Aeurias/NadeshikoSlimeVR/Misc/cases8111X.jpg

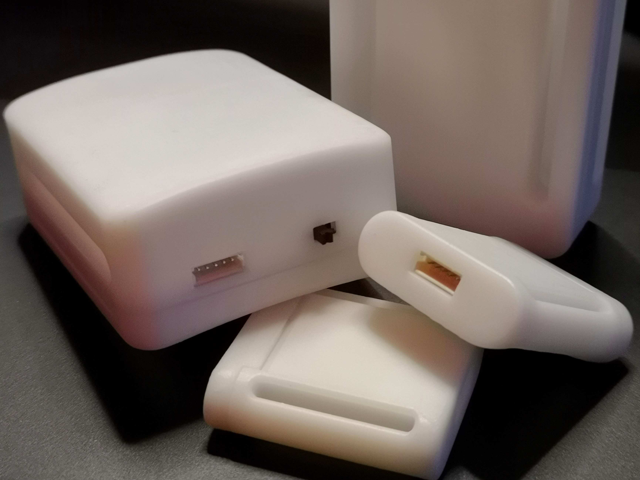
Misc/cases8111X.jpg
