Aeurias/NadeshikoSlimeVR/Misc/Extension-PCB-Front.png

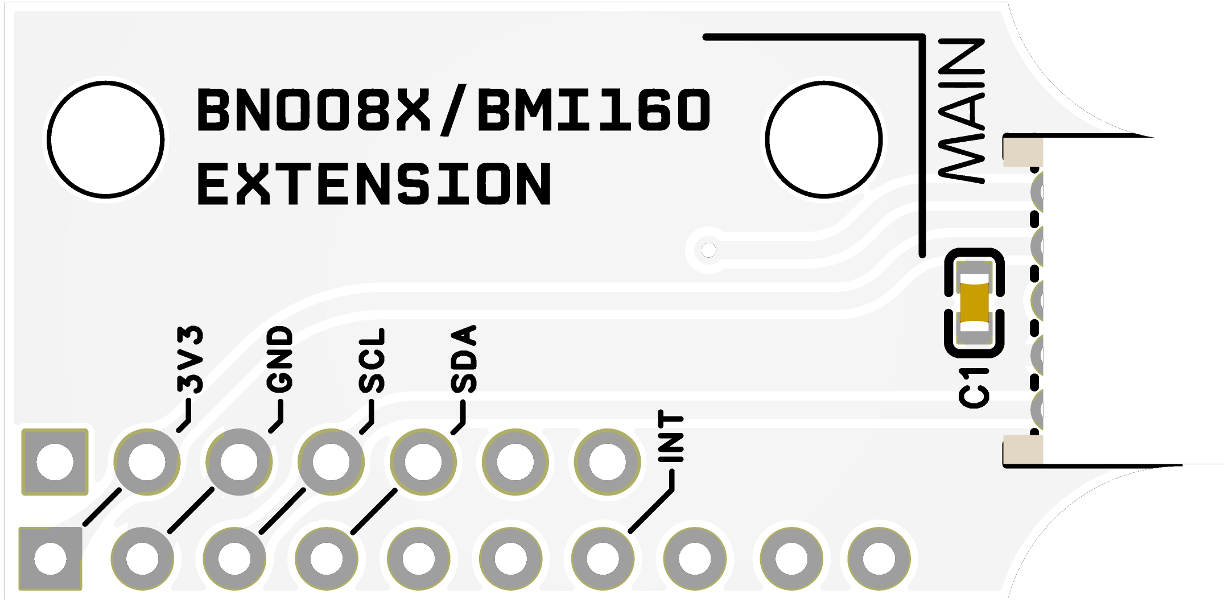
Misc/Extension-PCB-Front.png
