Aeurias/NadeshikoSlimeVR/Misc/PCBBack.png

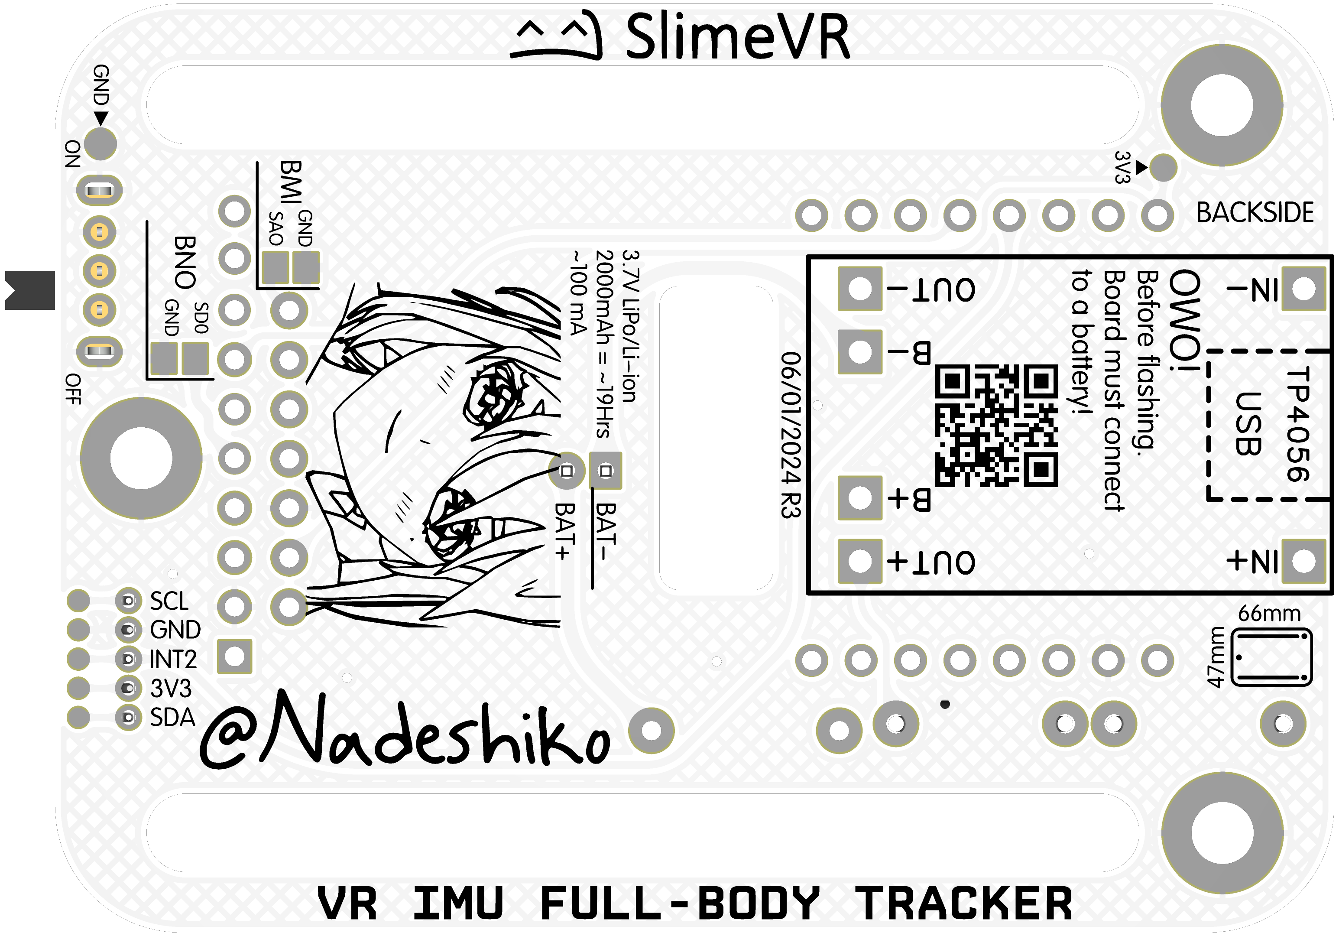
Misc/PCBBack.png
