Aeurias/NadeshikoSlimeVR/Misc/PCBFront.png

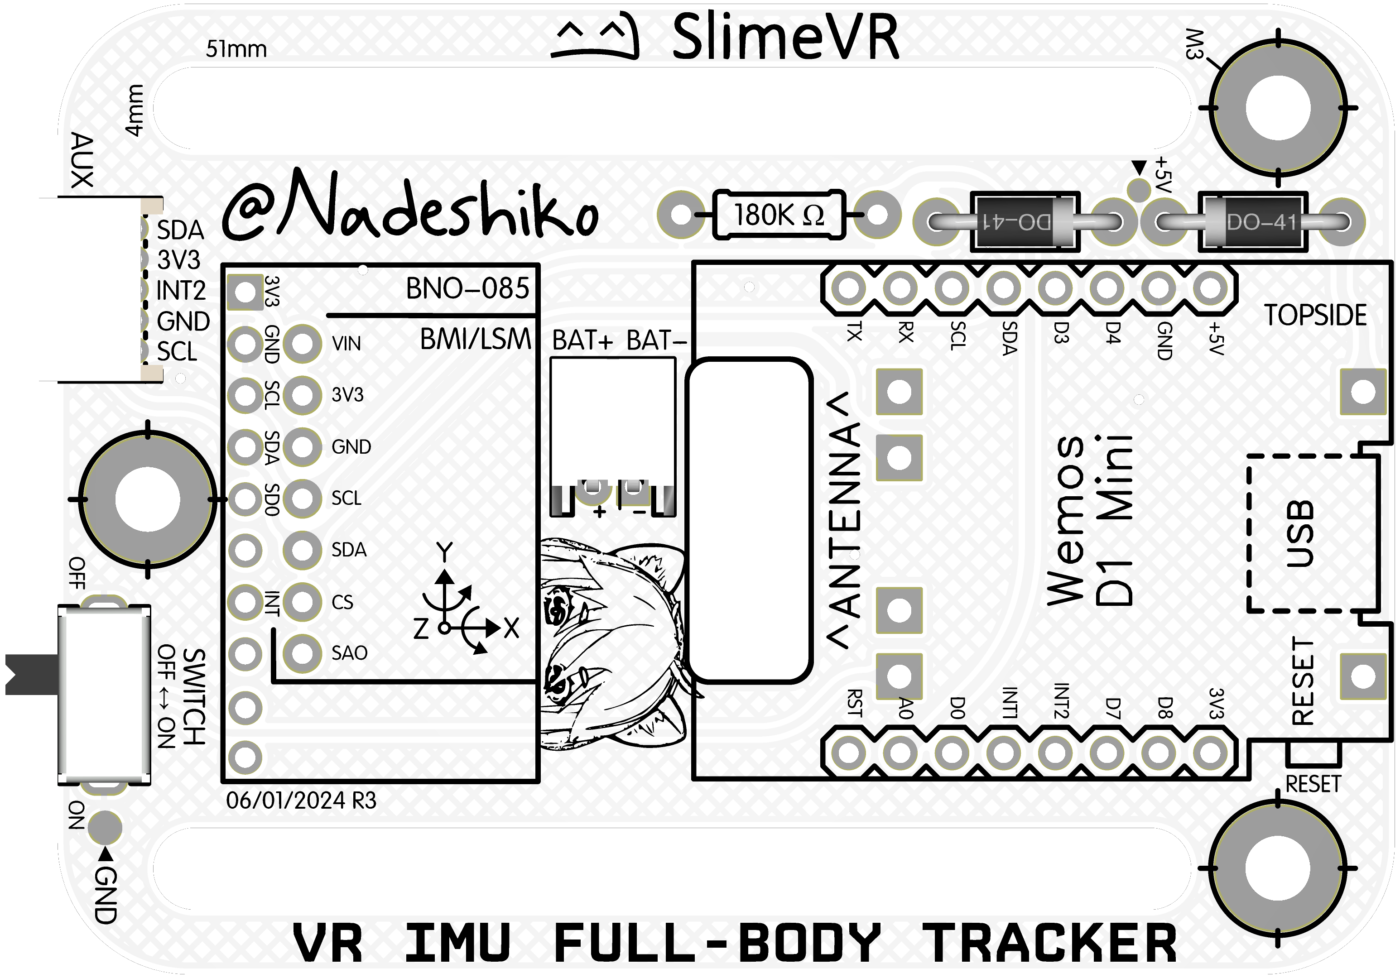
Misc/PCBFront.png
