Aeurias/NadeshikoSlimeVR/Misc/PlacementExample.png

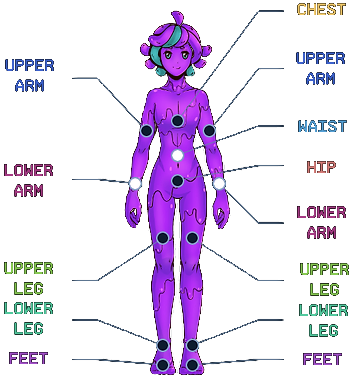
Misc/PlacementExample.png
