Aeurias/NadeshikoSlimeVR/Misc/PlacementOptions.png

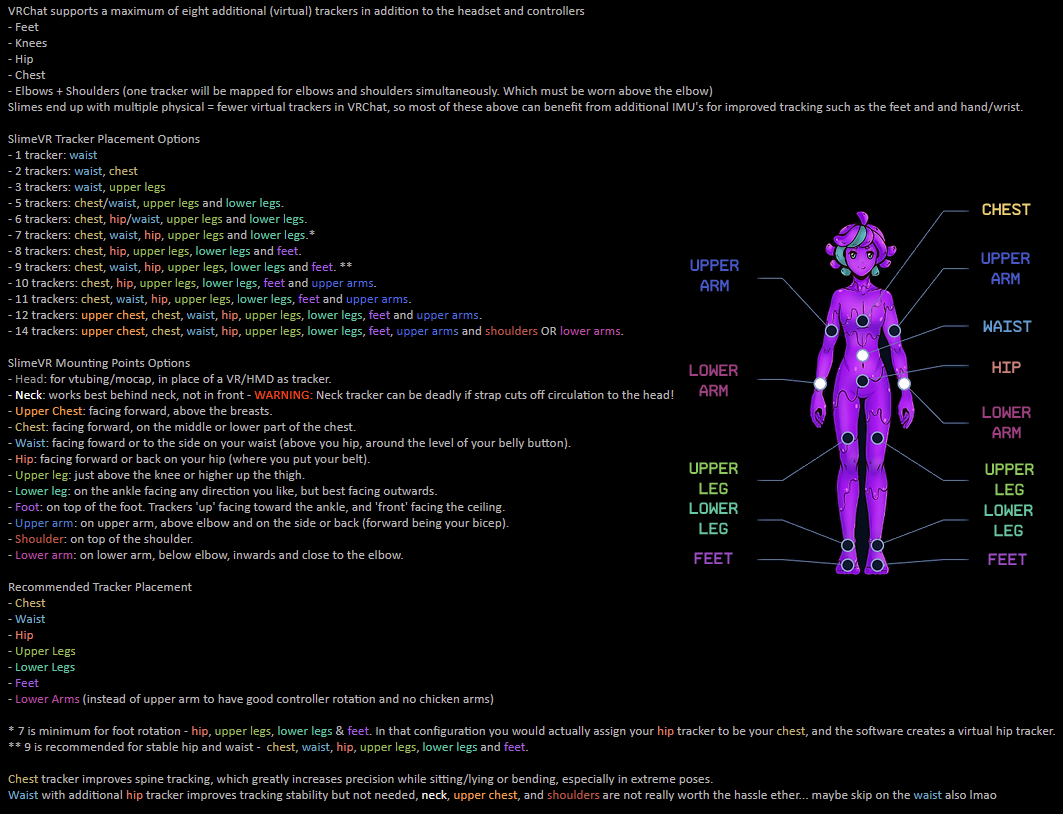
Misc/PlacementOptions.png
