Aeurias/NadeshikoSlimeVR/Misc/readmepreview1.png

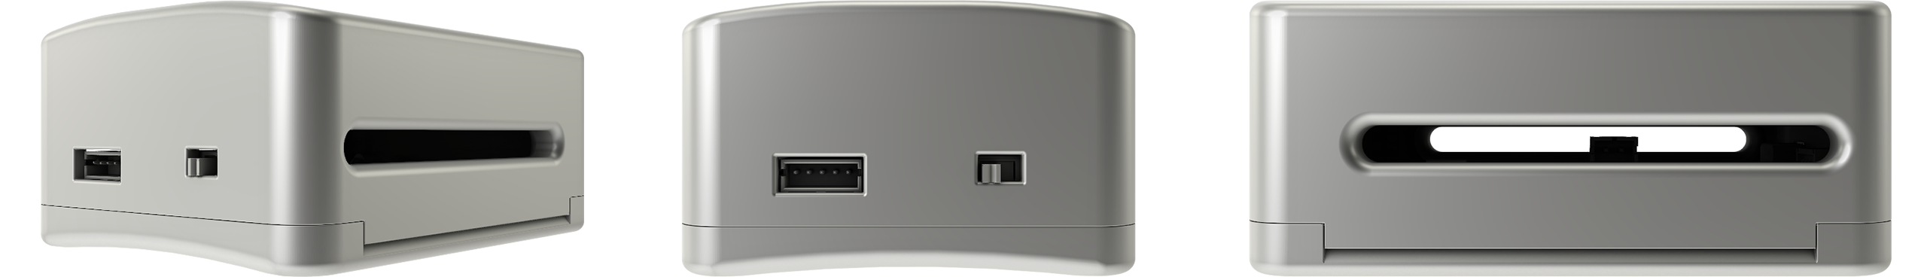
Misc/readmepreview1.png
