Aeurias/NadeshikoSlimeVR/R1/Previews/R1-18650-1.png

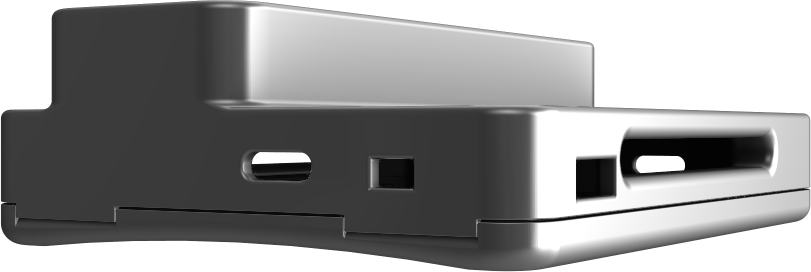
R1/Previews/R1-18650-1.png
