Aeurias/NadeshikoSlimeVR/R1/Previews/R1-18650-2.png

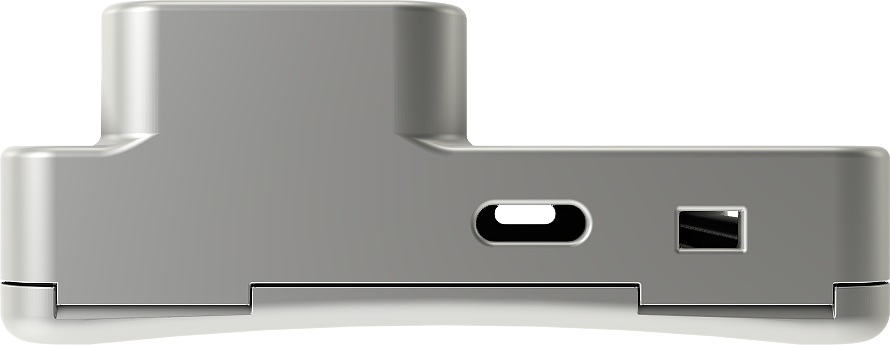
R1/Previews/R1-18650-2.png
