Aeurias/NadeshikoSlimeVR/R1/Previews/R1-18650-3.png

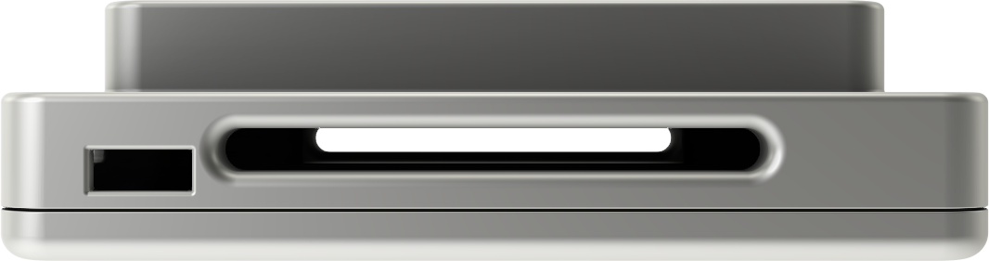
R1/Previews/R1-18650-3.png
