Aeurias/NadeshikoSlimeVR/R1/Previews/R1-LiPo-2.png

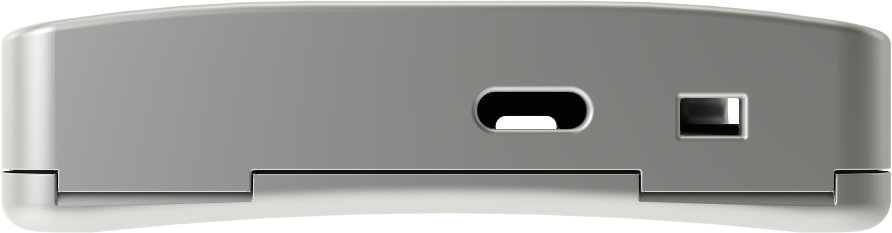
R1/Previews/R1-LiPo-2.png
