Aeurias/NadeshikoSlimeVR/R1/Previews/R1-LiPo-3.png

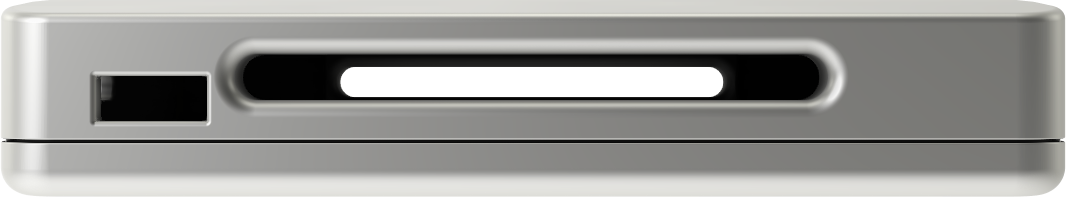
R1/Previews/R1-LiPo-3.png
