Aeurias/NadeshikoSlimeVR/R1/Previews/R1-PCB-Back.png

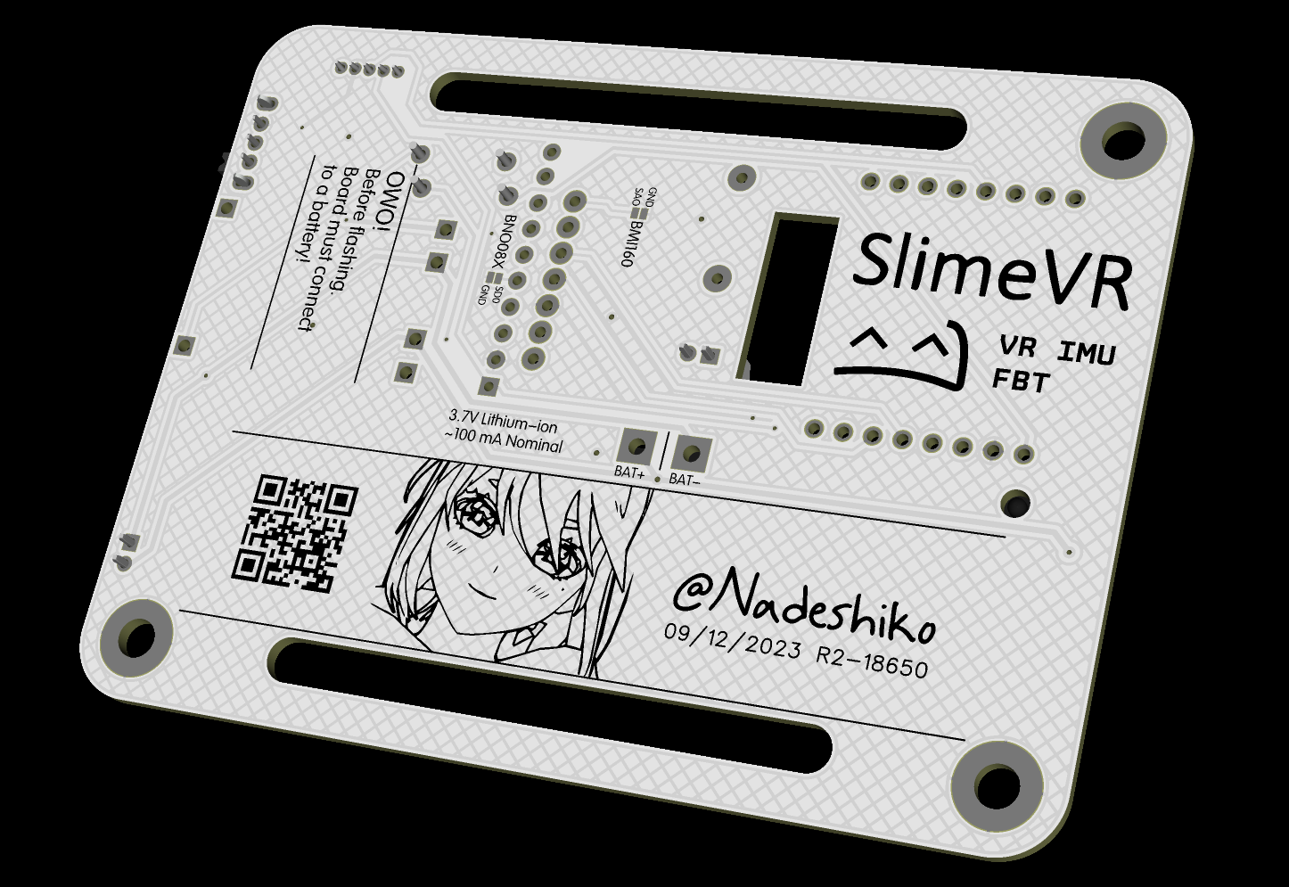
R1/Previews/R1-PCB-Back.png
