Aeurias/NadeshikoSlimeVR/R1/Previews/R1-PCB-Front.png

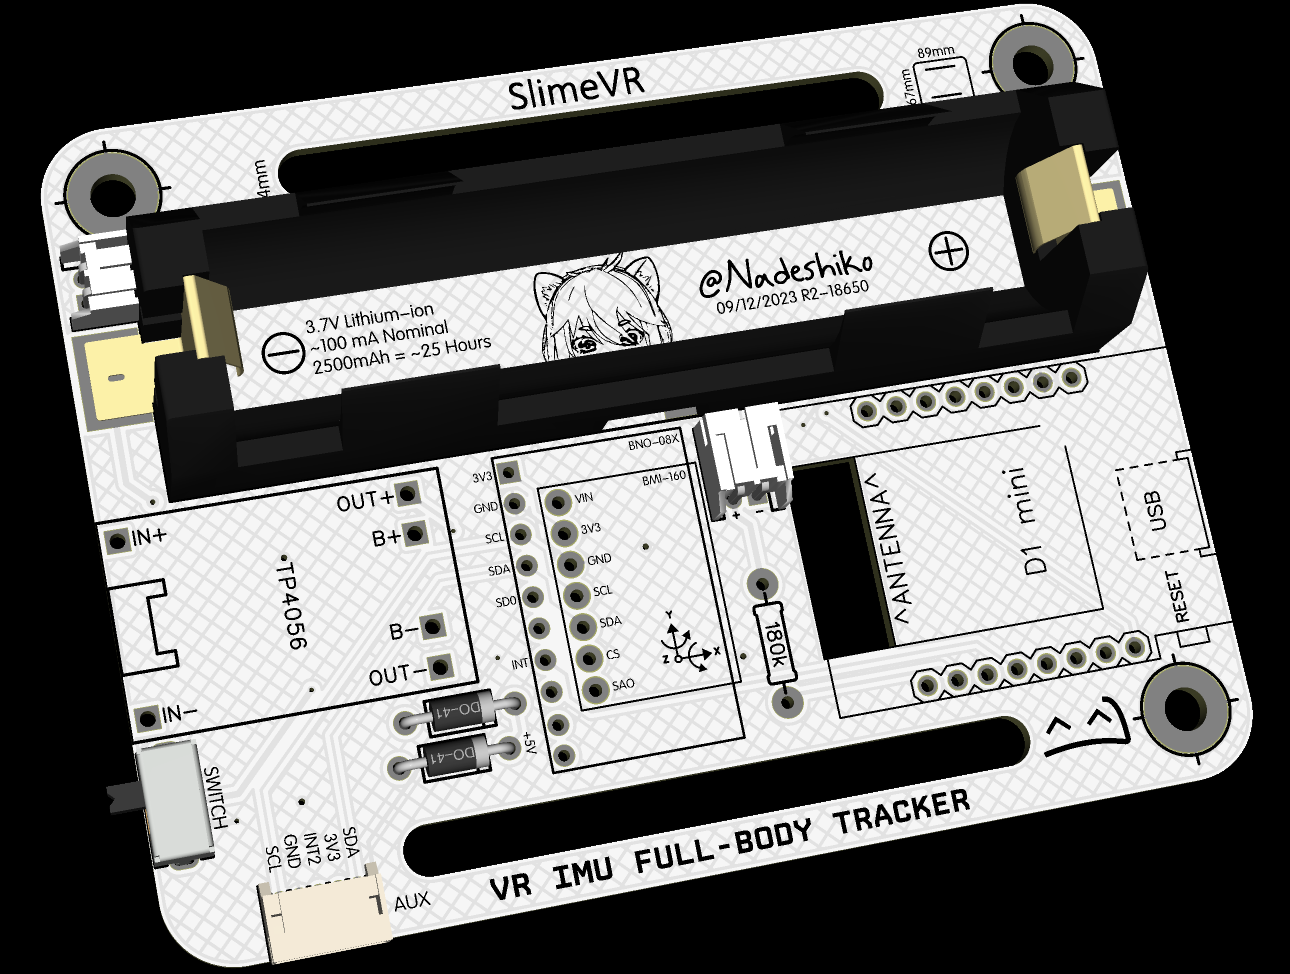
R1/Previews/R1-PCB-Front.png
