Aeurias/NadeshikoSlimeVR/R2 Mini/Previews/R2Mini-103450-3.png

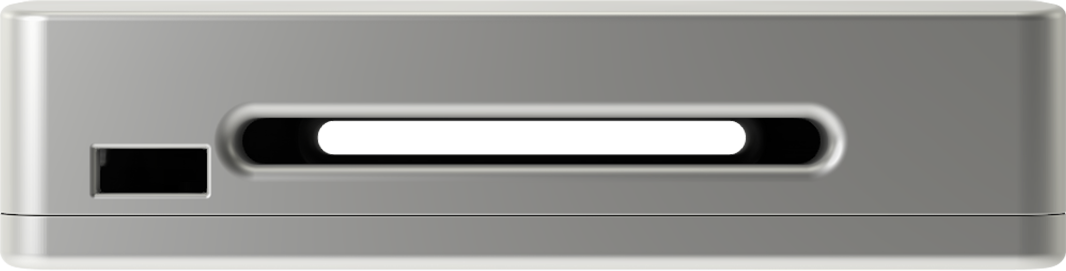
R2 Mini/Previews/R2Mini-103450-3.png
