Aeurias/NadeshikoSlimeVR/R2 Mini/Previews/R2Mini-503450-2.png

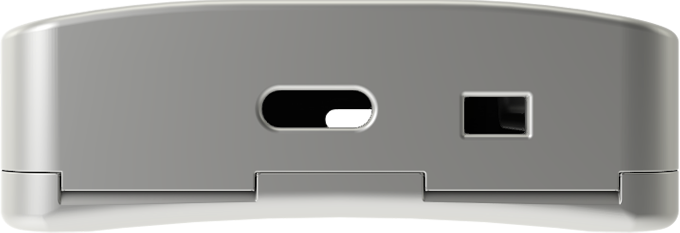
R2 Mini/Previews/R2Mini-503450-2.png
