Aeurias/NadeshikoSlimeVR/R2 Mini/Previews/R2Mini-503450-3.png

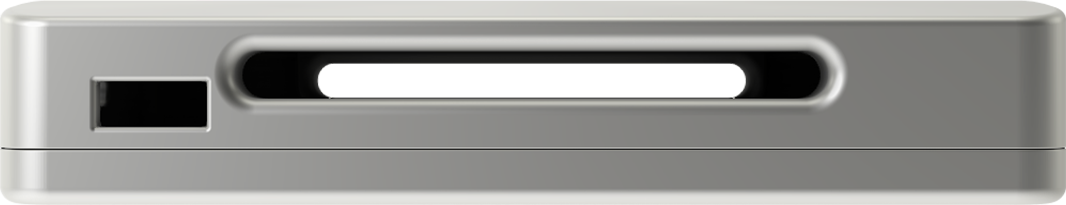
R2 Mini/Previews/R2Mini-503450-3.png
