Aeurias/NadeshikoSlimeVR/R2 Mini/Previews/R2Mini-PCB-Back.png

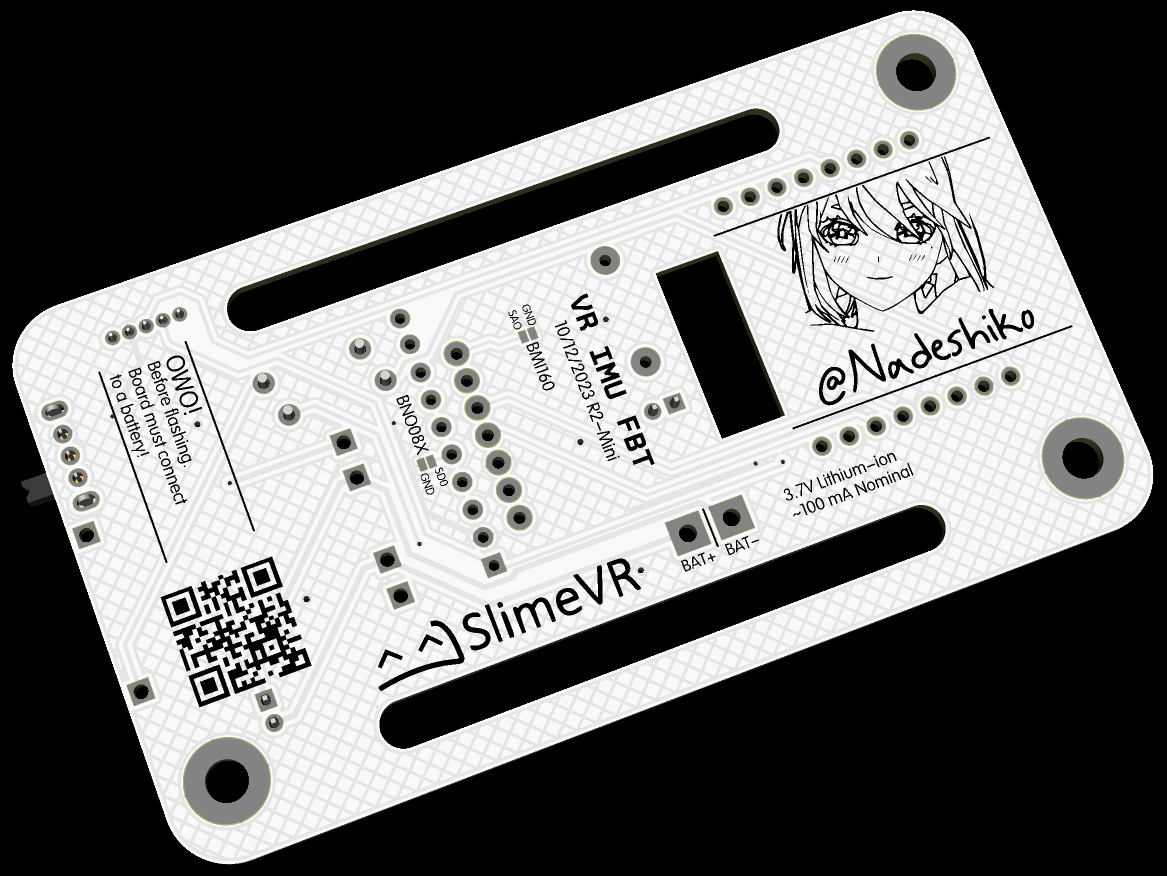
R2 Mini/Previews/R2Mini-PCB-Back.png
