Aeurias/NadeshikoSlimeVR/R2 Mini/Previews/R2Mini-PCB-Front.png

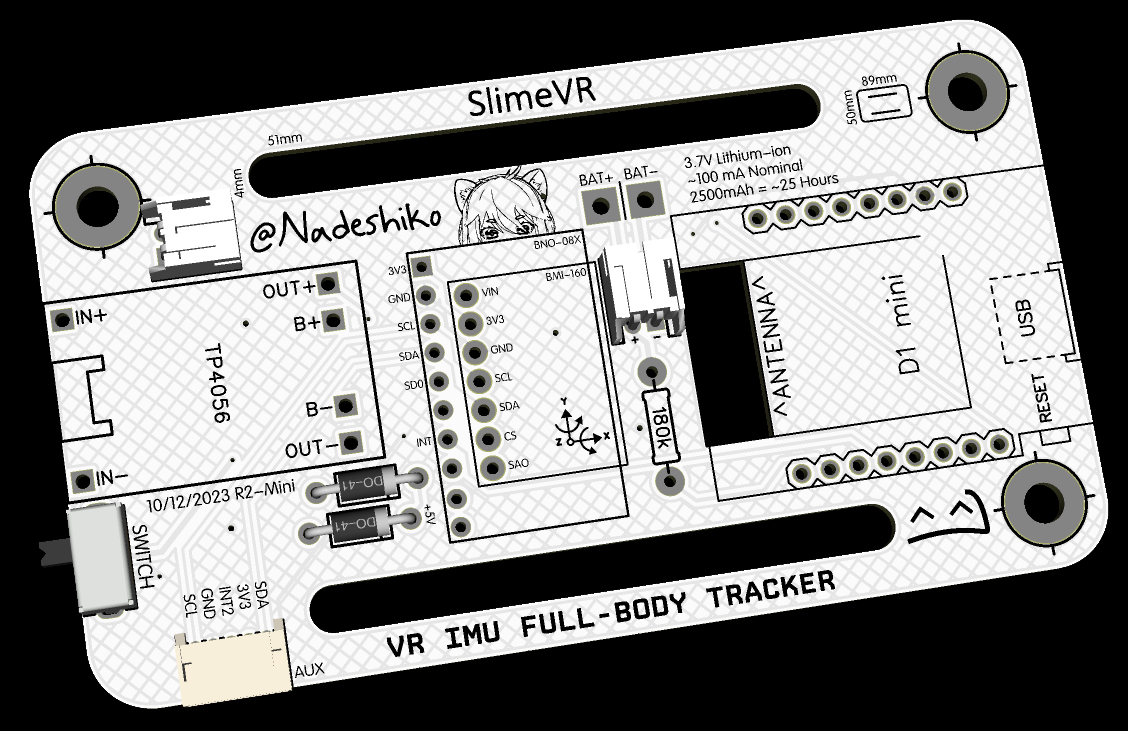
R2 Mini/Previews/R2Mini-PCB-Front.png
