Aeurias/NadeshikoSlimeVR/Tracker Extension/Previews/Extension-1.png

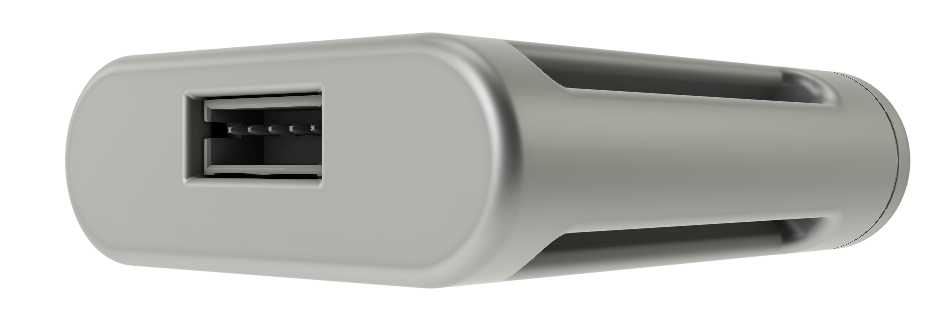
Tracker Extension/Previews/Extension-1.png
