Aeurias/NadeshikoSlimeVR/Tracker Extension/Previews/Extension-2.png

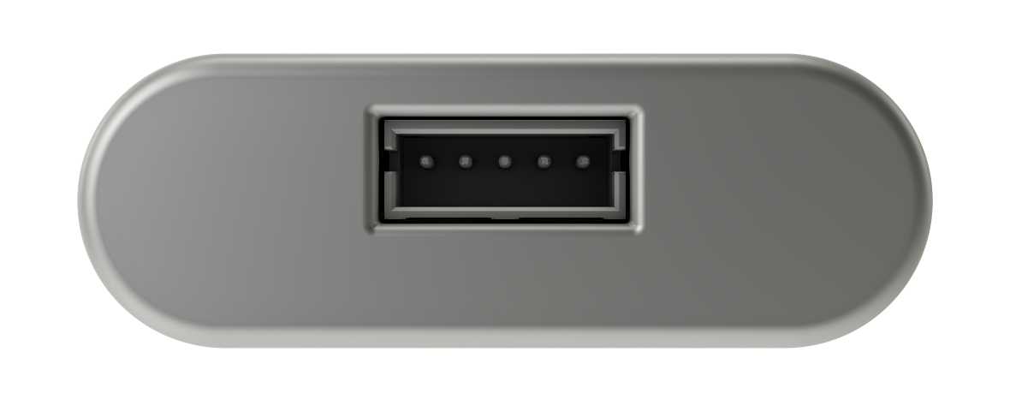
Tracker Extension/Previews/Extension-2.png
