Aeurias/NadeshikoSlimeVR/Tracker Extension/Previews/Extension-3.png

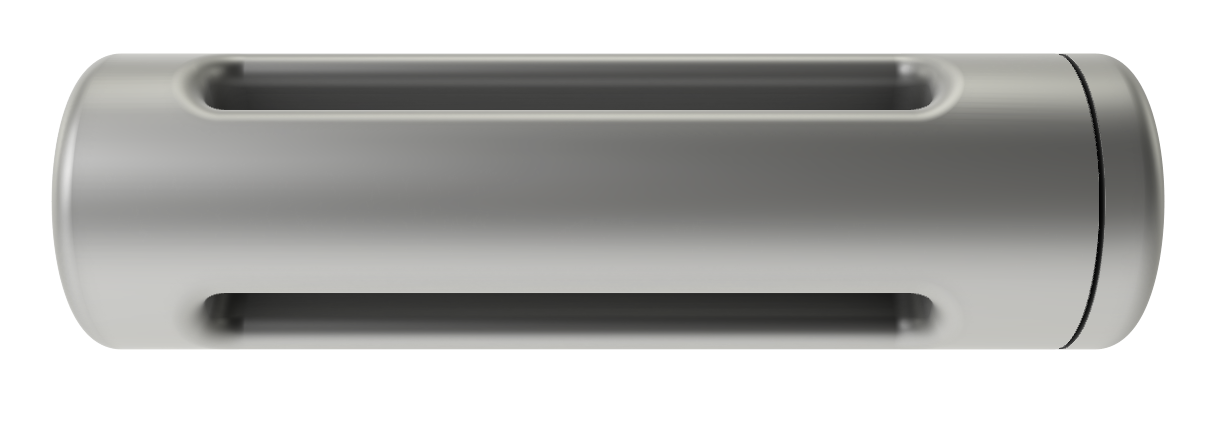
Tracker Extension/Previews/Extension-3.png
