Aeurias/NadeshikoSlimeVR/Tracker Extension/Previews/SlimeVRNadeshikoExtension_PREVIEW-1.png

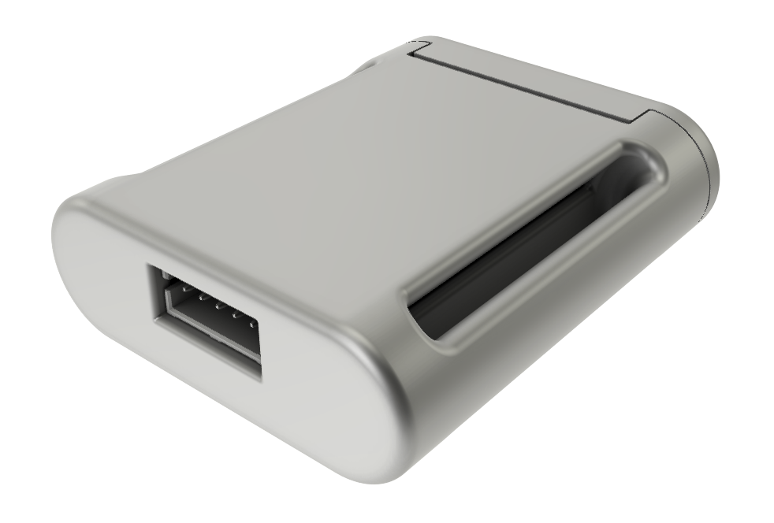
Tracker Extension/Previews/SlimeVRNadeshikoExtension_PREVIEW-1.png
