Aeurias/NadeshikoSlimeVR/Tracker Extension/Previews/SlimeVRNadeshikoExtension_PREVIEW-2.png

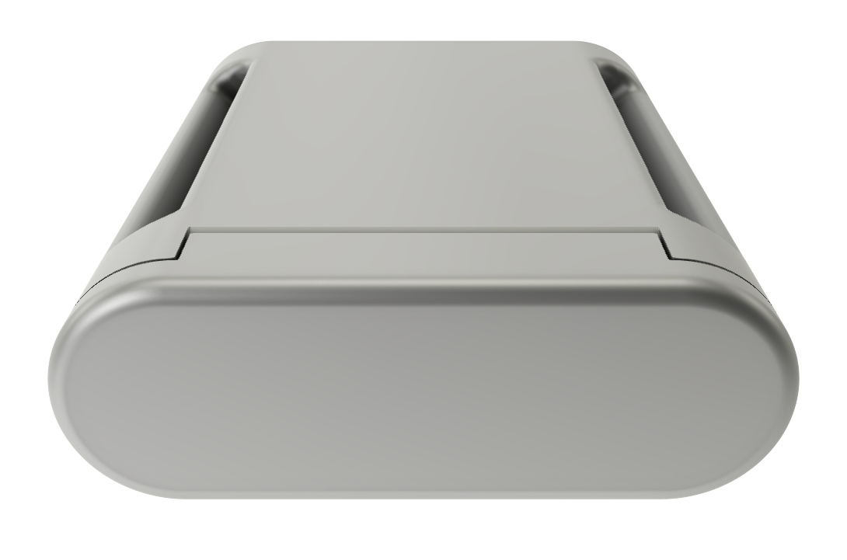
Tracker Extension/Previews/SlimeVRNadeshikoExtension_PREVIEW-2.png
