Aeurias/NadeshikoSlimeVR/Tracker Main/Previews/Back.png

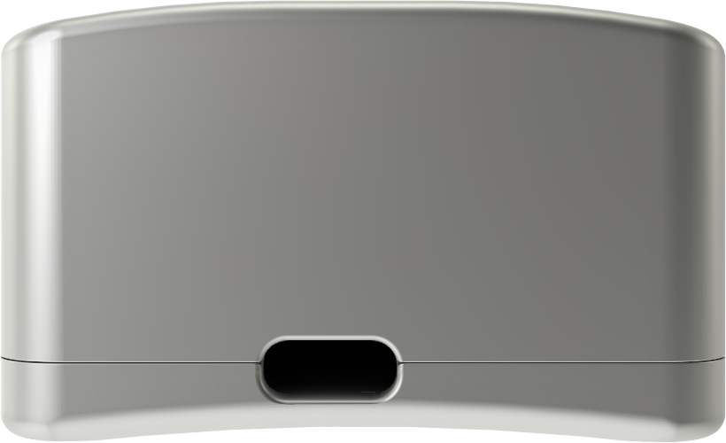
Tracker Main/Previews/Back.png
