Aeurias/NadeshikoSlimeVR/Tracker Main/Previews/CAD.jpg

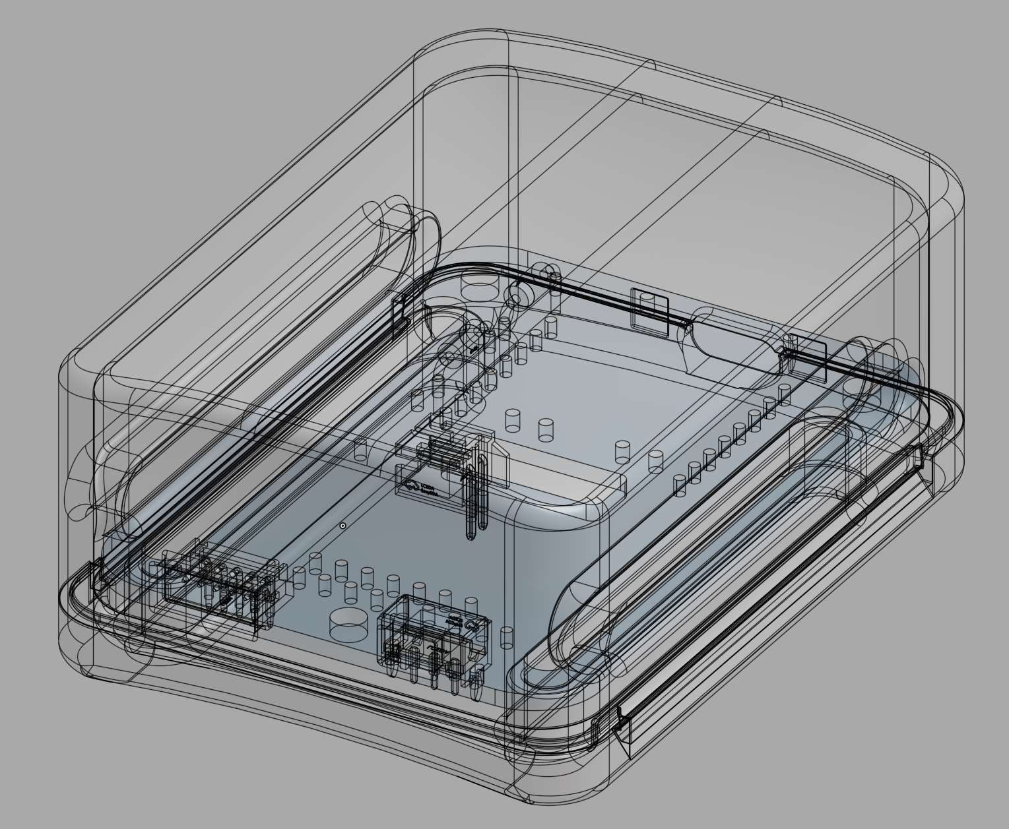
Tracker Main/Previews/CAD.jpg
