Aeurias/NadeshikoSlimeVR/Tracker Main/Previews/Front.png

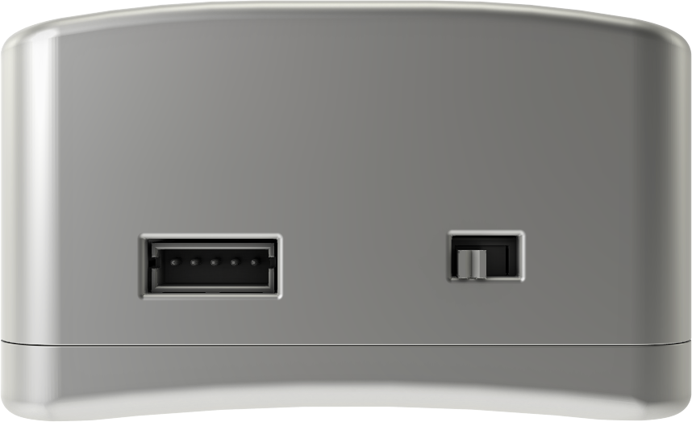
Tracker Main/Previews/Front.png
