Aeurias/NadeshikoSlimeVR/Tracker Main/Previews/FrontRight.png

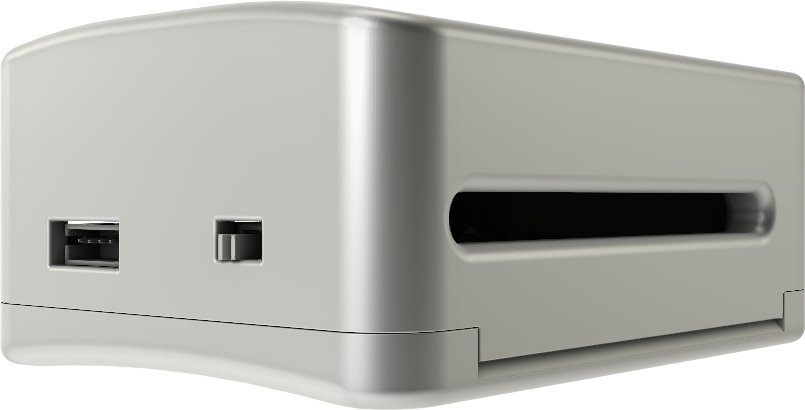
Tracker Main/Previews/FrontRight.png
