Aeurias/NadeshikoSlimeVR/Tracker Main/Previews/FrontRightBelow.png

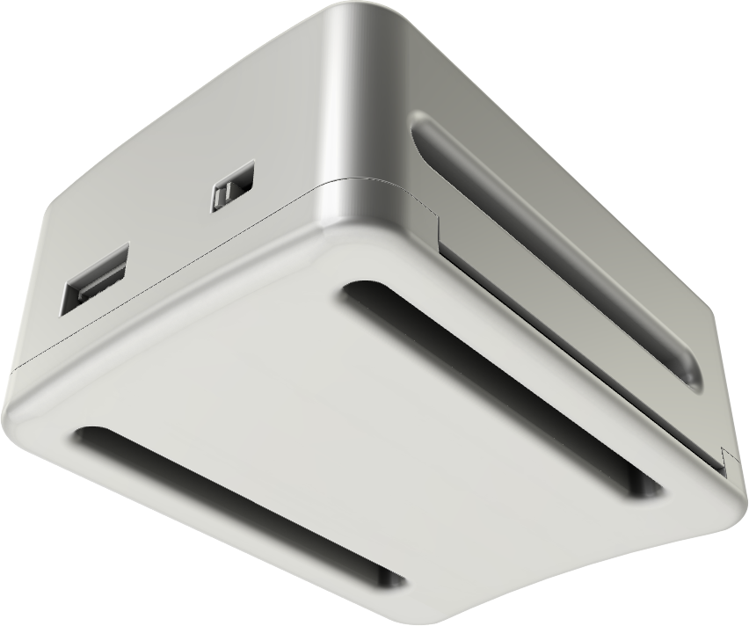
Tracker Main/Previews/FrontRightBelow.png
