Aeurias/NadeshikoSlimeVR/Tracker Main/Previews/Right.png

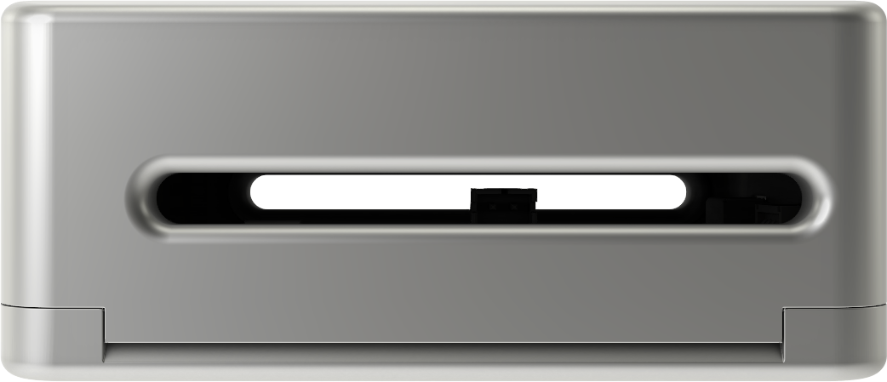
Tracker Main/Previews/Right.png
