Aeurias/NadeshikoSlimeVR/Tracker Supermini/Previews/NadeshikoMini-PREVIEW0.png

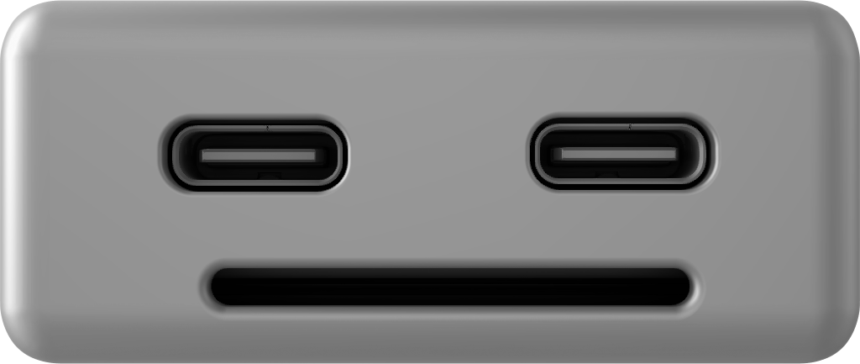
Tracker Supermini/Previews/NadeshikoMini-PREVIEW0.png
