Aeurias/NadeshikoSlimeVR/Tracker Supermini/Previews/NadeshikoMini-PREVIEW1.png

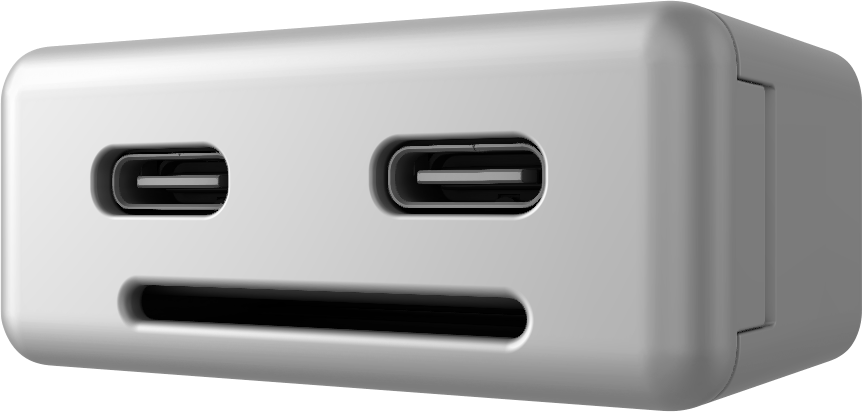
Tracker Supermini/Previews/NadeshikoMini-PREVIEW1.png
