Aeurias/NadeshikoSlimeVR/Tracker Supermini/Previews/NadeshikoMini-PREVIEW2.png

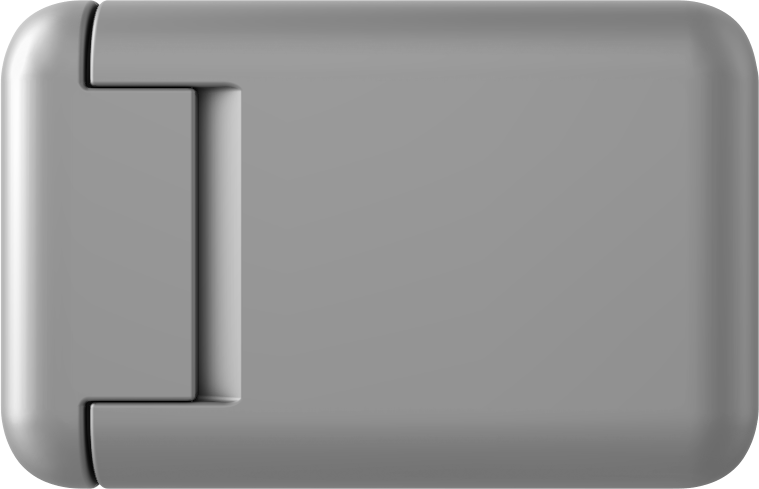
Tracker Supermini/Previews/NadeshikoMini-PREVIEW2.png
