Aeurias/NadeshikoSlimeVR/Tracker Supermini/Previews/NadeshikoMini-PREVIEW3.png

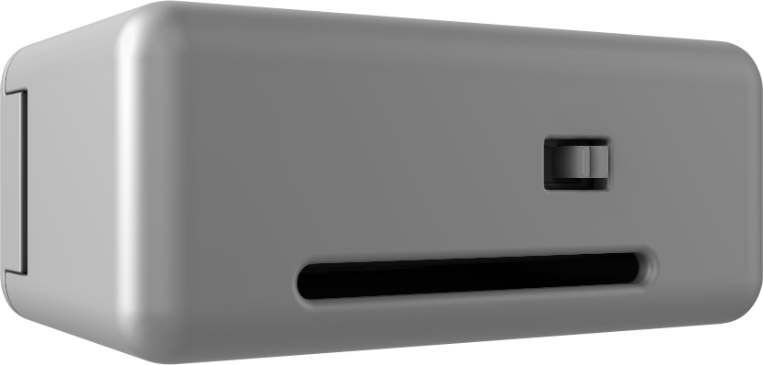
Tracker Supermini/Previews/NadeshikoMini-PREVIEW3.png
