Aeurias/NadeshikoSlimeVR/Tracker Supermini/Previews/NadeshikoMini-PREVIEW4.png

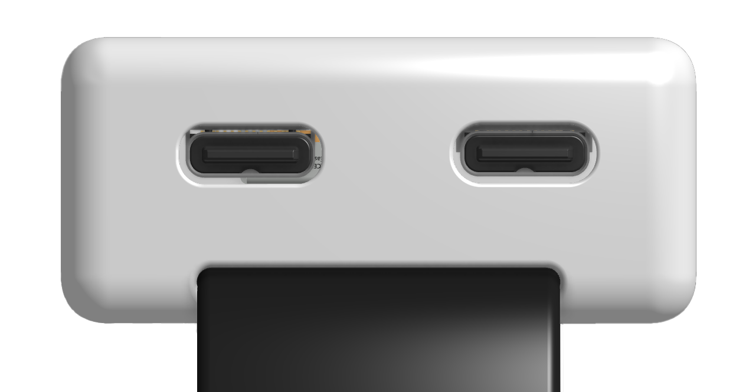
Tracker Supermini/Previews/NadeshikoMini-PREVIEW4.png
