Aeurias/NadeshikoSlimeVR/Tracker Supermini/Previews/NadeshikoSupermini-Double-PREVIEW1.png

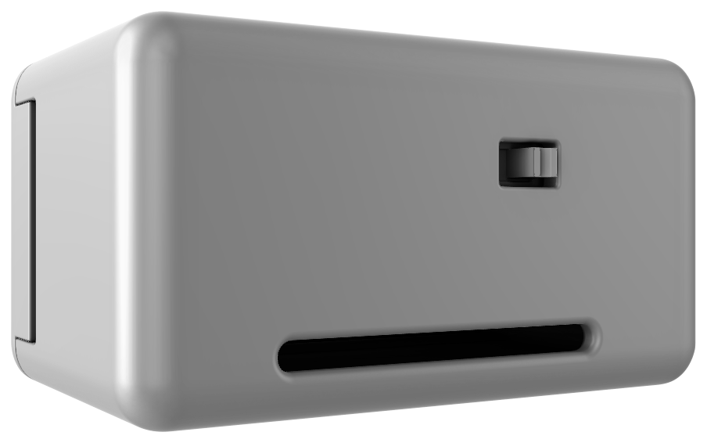
Tracker Supermini/Previews/NadeshikoSupermini-Double-PREVIEW1.png
