Aeurias/NadeshikoSlimeVR/Tracker Supermini/Previews/NadeshikoSupermini-Double-PREVIEW2.png

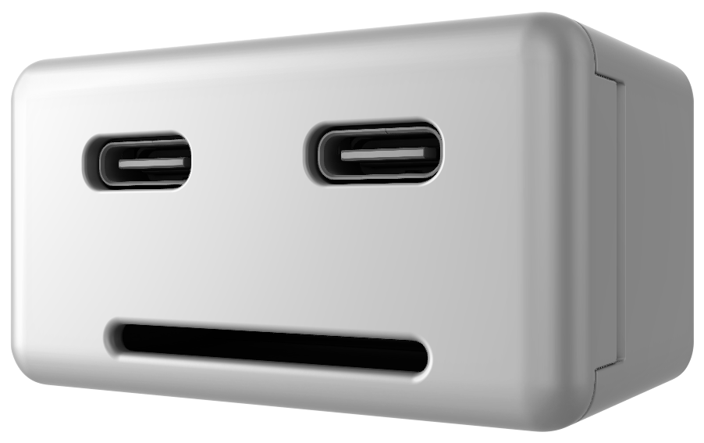
Tracker Supermini/Previews/NadeshikoSupermini-Double-PREVIEW2.png
