Aeurias/NadeshikoSlimeVR/Tracker Supermini/Previews/WristPreview.png

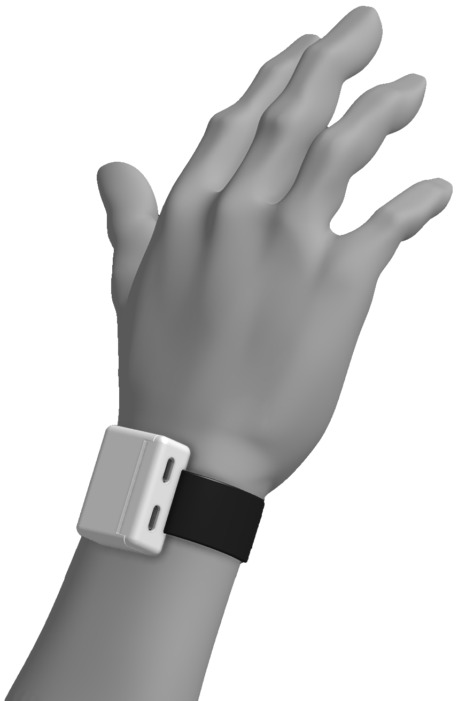
Tracker Supermini/Previews/WristPreview.png
