Aeurias/NadeshikoSlimeVR/Misc/Assembly/Components/1.jpg

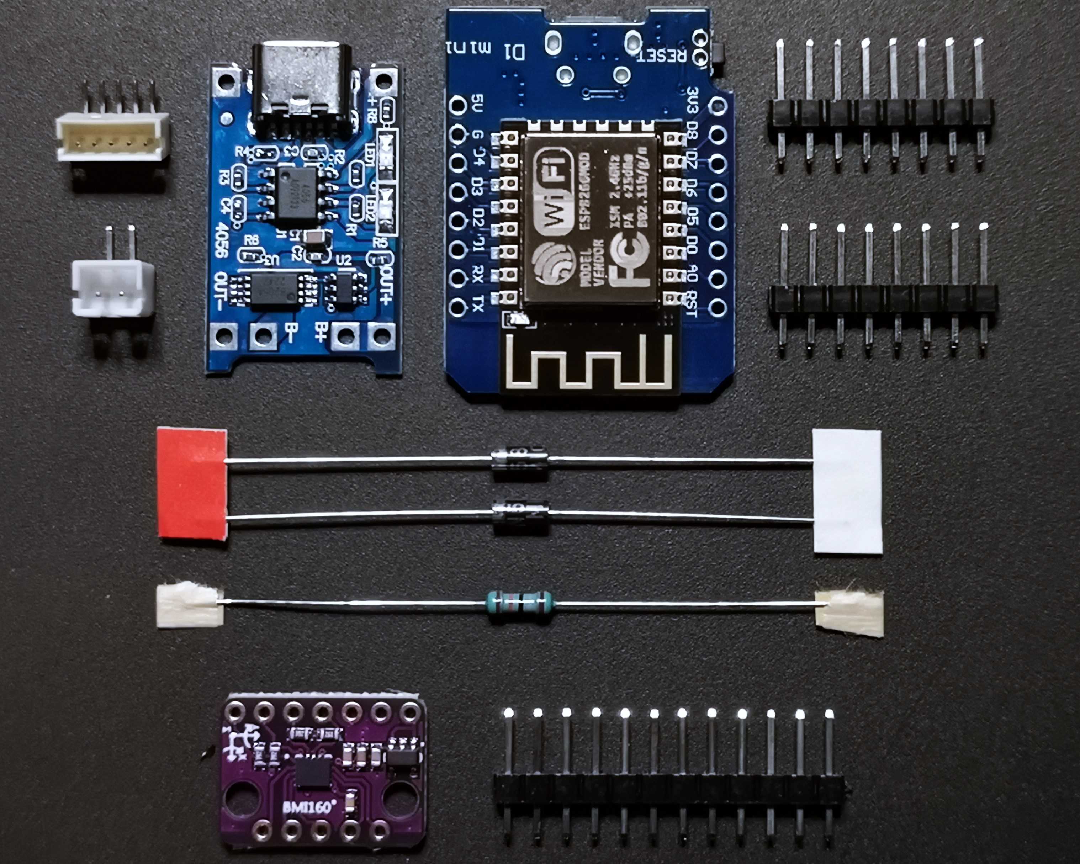
Misc/Assembly/Components/1.jpg
