Aeurias/NadeshikoSlimeVR/Tracker Extension/3D Print STL/OrderingCases.png

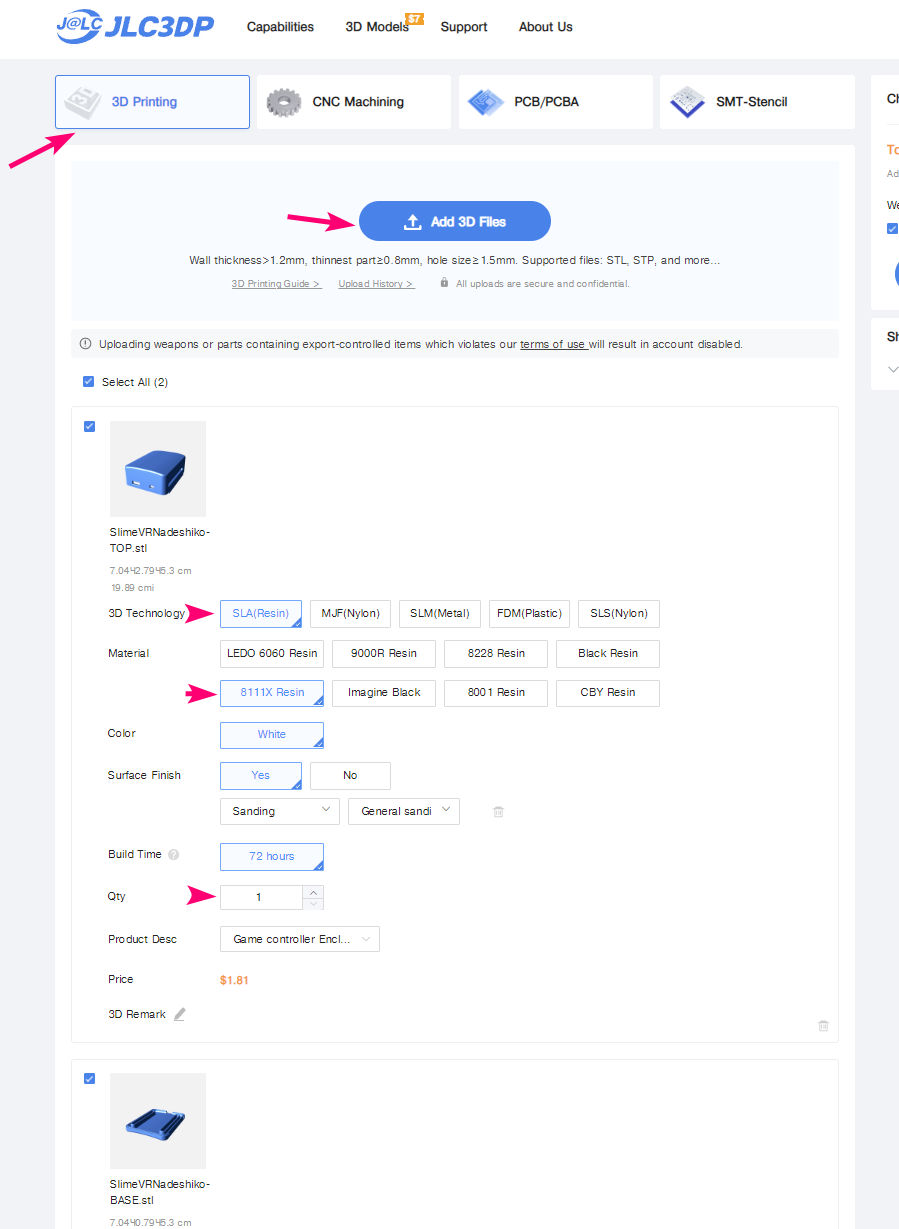
Tracker Extension/3D Print STL/OrderingCases.png
