Aeurias/NadeshikoSlimeVR/Misc/Assembly/PCB/bothside.jpg

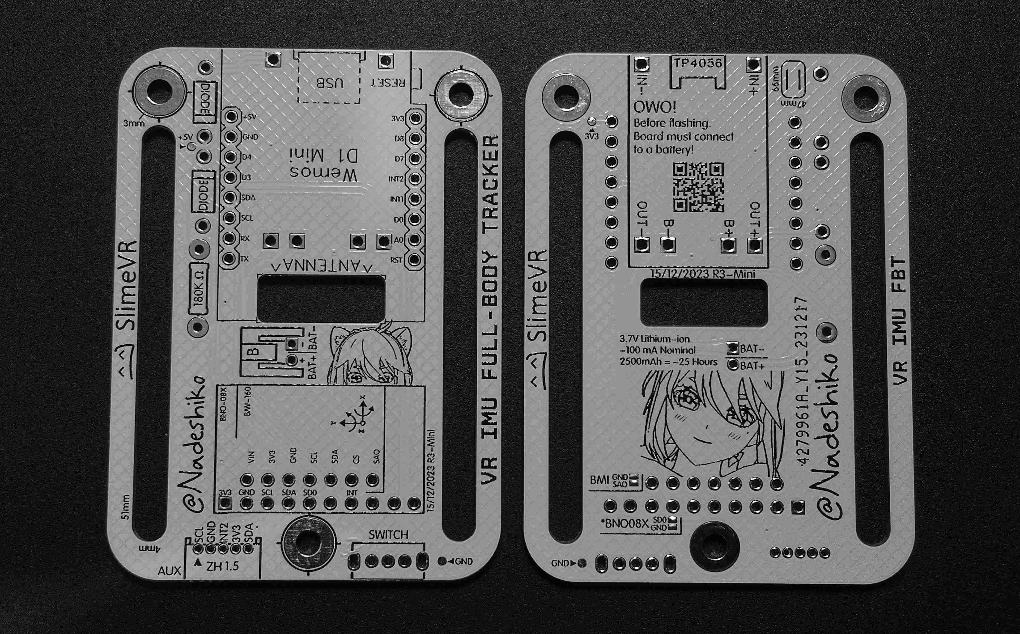
Misc/Assembly/PCB/bothside.jpg
