Aeurias/NadeshikoSlimeVR/Misc/Assembly/Step1-ResDio-Bend/1.jpg

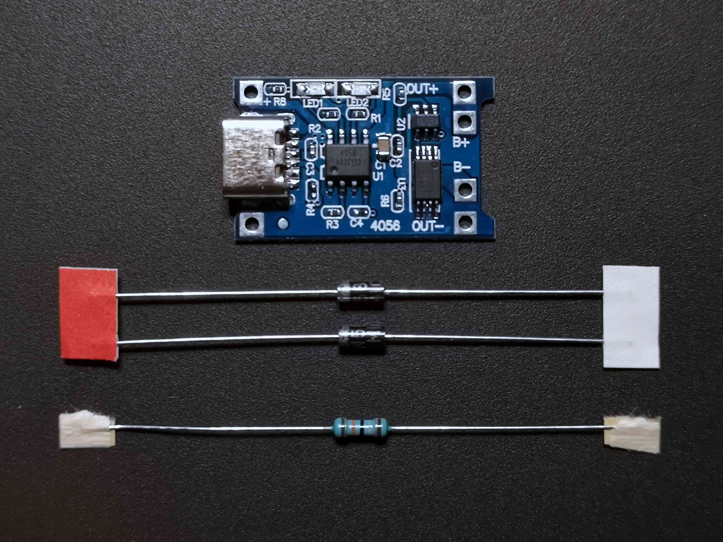
Misc/Assembly/Step1-ResDio-Bend/1.jpg
