Aeurias/NadeshikoSlimeVR/Misc/Assembly/Step1-ResDio-Bend/2.jpg

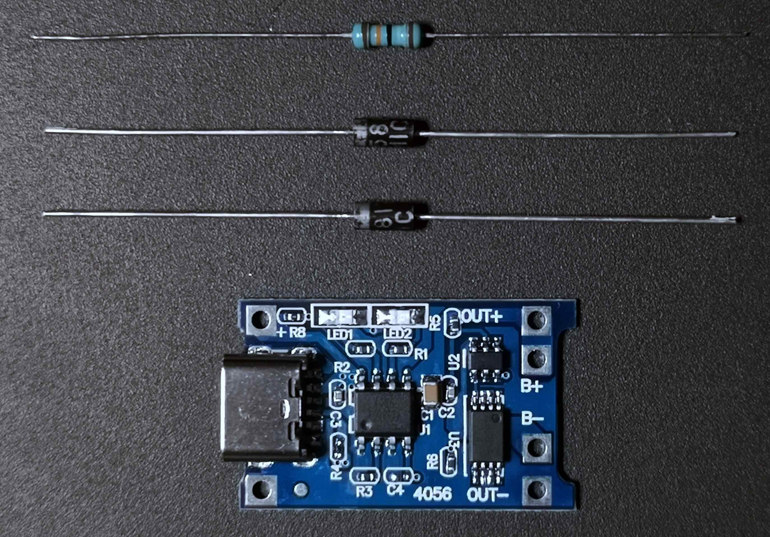
Misc/Assembly/Step1-ResDio-Bend/2.jpg
