Aeurias/NadeshikoSlimeVR/Misc/Assembly/Step-2-ResDio-1/1.jpg

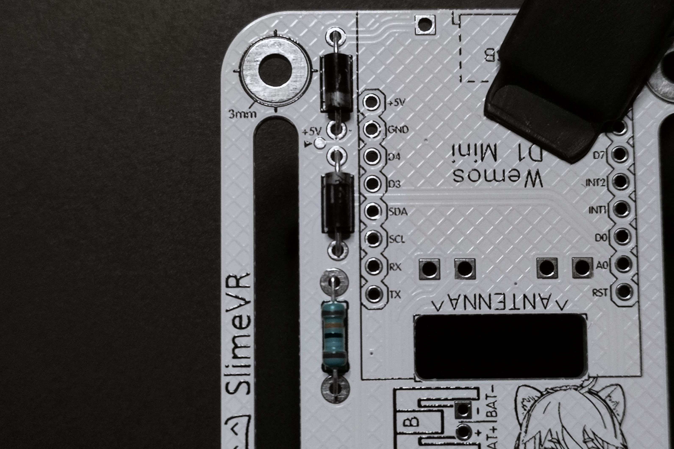
Misc/Assembly/Step-2-ResDio-1/1.jpg
