Aeurias/NadeshikoSlimeVR/Misc/Assembly/Step-2-ResDio-1/2.jpg

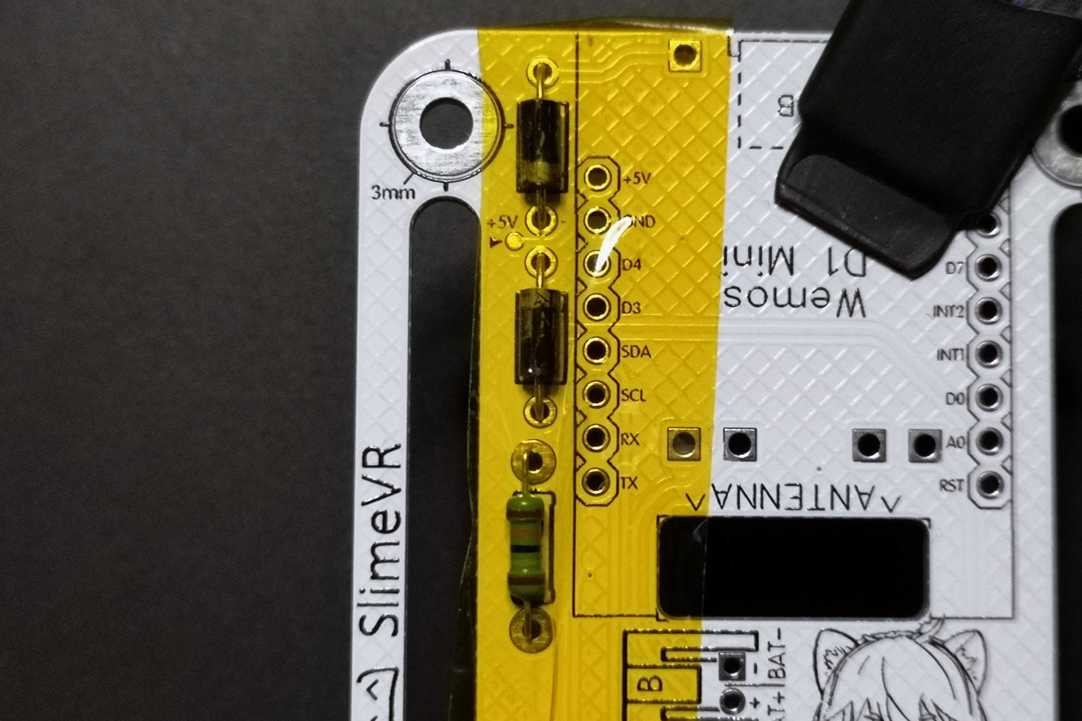
Misc/Assembly/Step-2-ResDio-1/2.jpg
