Aeurias/NadeshikoSlimeVR/Misc/Assembly/Step-2-ResDio-1/4.jpg

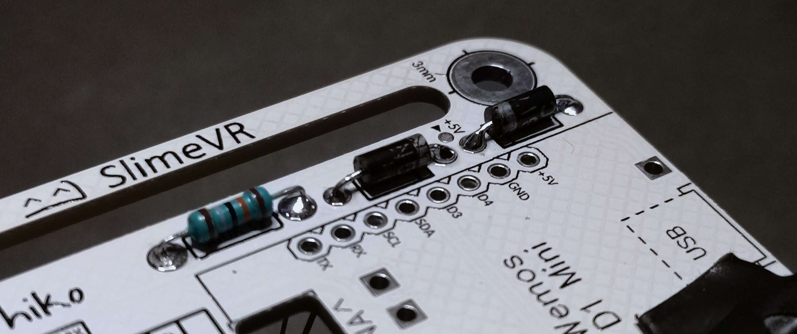
Misc/Assembly/Step-2-ResDio-1/4.jpg
