Aeurias/NadeshikoSlimeVR/Misc/Assembly/Step-3-ResDio-2/1.jpg

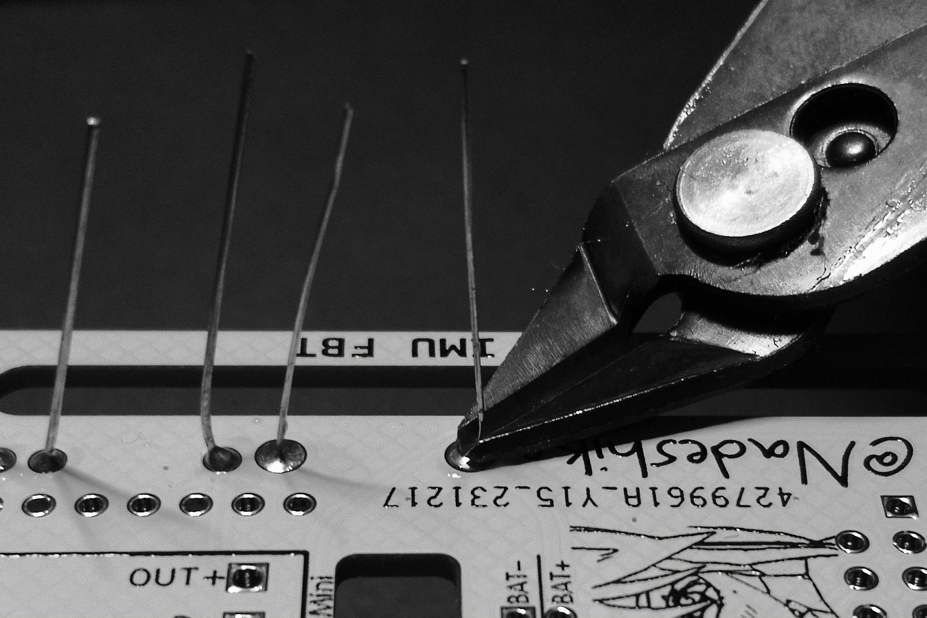
Misc/Assembly/Step-3-ResDio-2/1.jpg
