Aeurias/NadeshikoSlimeVR/Misc/Assembly/Step-3-ResDio-2/2.jpg

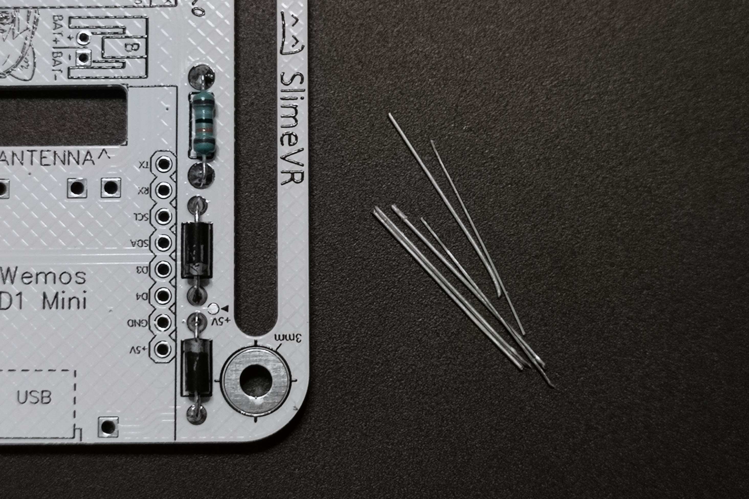
Misc/Assembly/Step-3-ResDio-2/2.jpg
