Aeurias/NadeshikoSlimeVR/Misc/Assembly/Step-4-TP4056/00.jpg

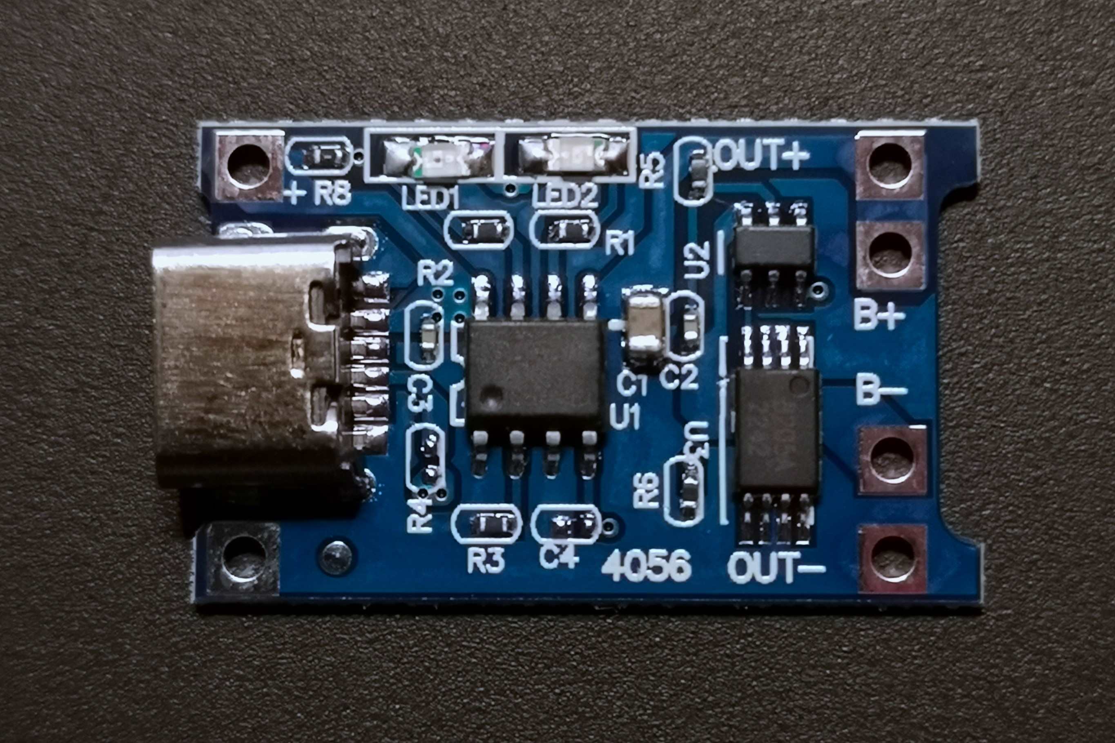
Misc/Assembly/Step-4-TP4056/00.jpg
