Aeurias/NadeshikoSlimeVR/Misc/Assembly/Step-4-TP4056/0.jpg

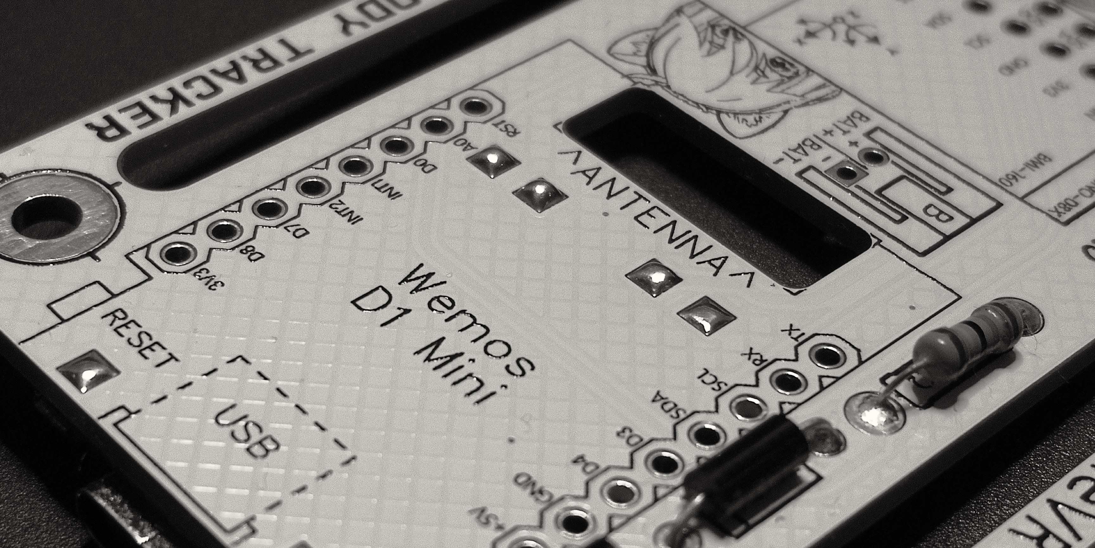
Misc/Assembly/Step-4-TP4056/0.jpg
