Aeurias/NadeshikoSlimeVR/Misc/Assembly/Step-4-TP4056/1.jpg

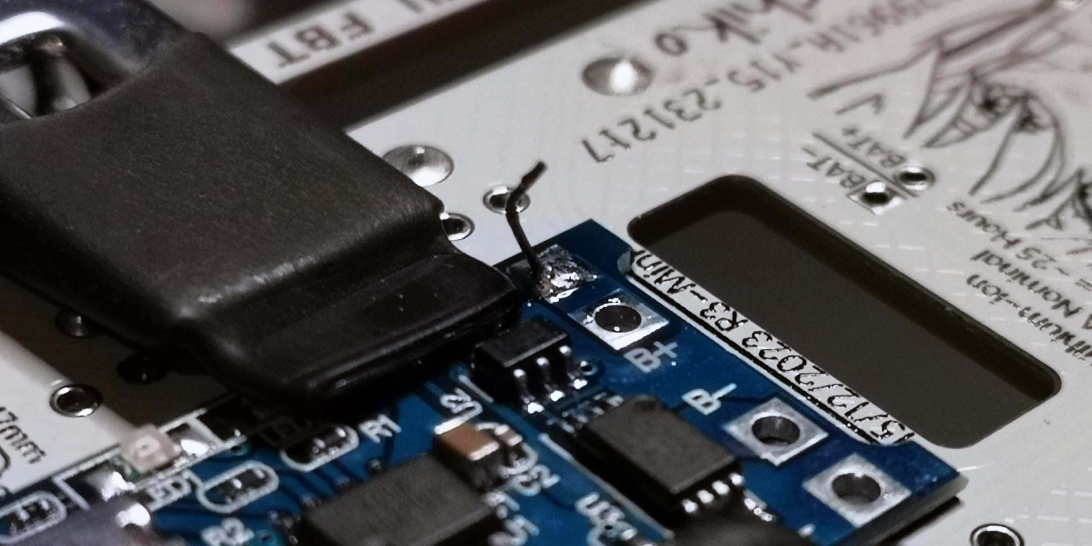
Misc/Assembly/Step-4-TP4056/1.jpg
