Aeurias/NadeshikoSlimeVR/Misc/Assembly/Step-4-TP4056/2.jpg

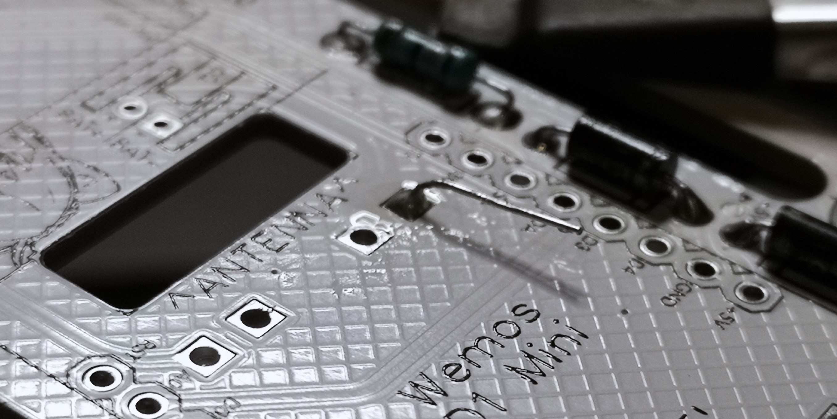
Misc/Assembly/Step-4-TP4056/2.jpg
