Aeurias/NadeshikoSlimeVR/Misc/Assembly/Step-4-TP4056/3.jpg

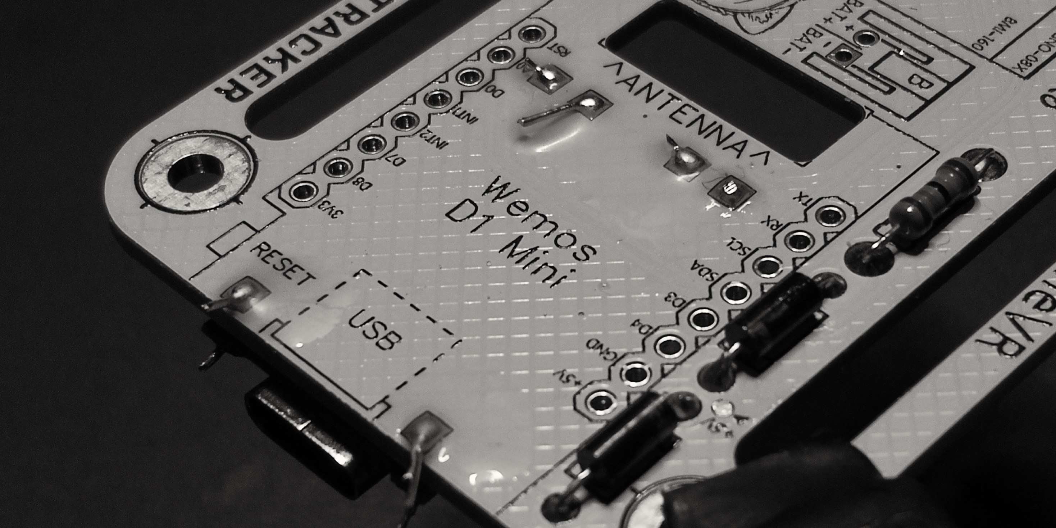
Misc/Assembly/Step-4-TP4056/3.jpg
