Aeurias/NadeshikoSlimeVR/Misc/Assembly/Step-4-TP4056/5.jpg

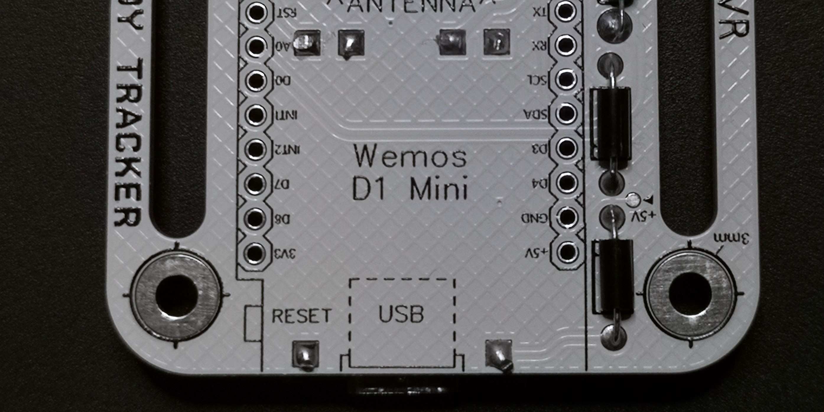
Misc/Assembly/Step-4-TP4056/5.jpg
