Aeurias/NadeshikoSlimeVR/Misc/Assembly/Step-4-TP4056/6.jpg

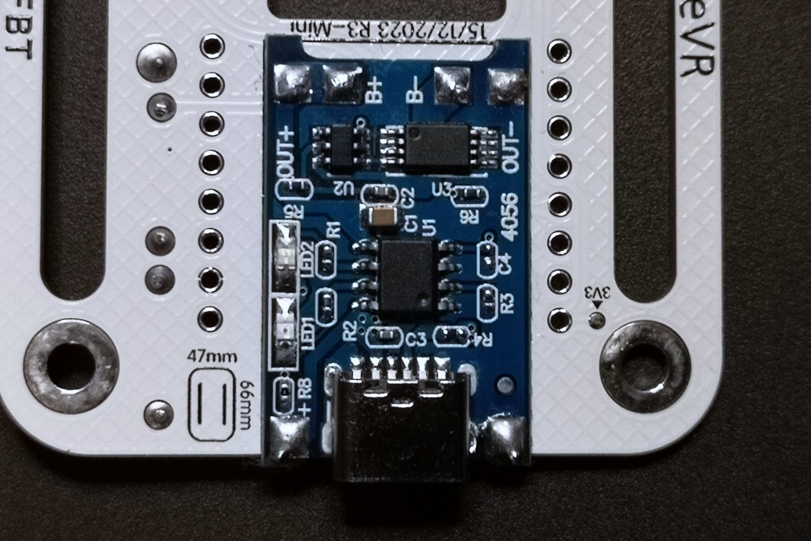
Misc/Assembly/Step-4-TP4056/6.jpg
