Aeurias/NadeshikoSlimeVR/Misc/Assembly/Step-5-2Pin/1.jpg

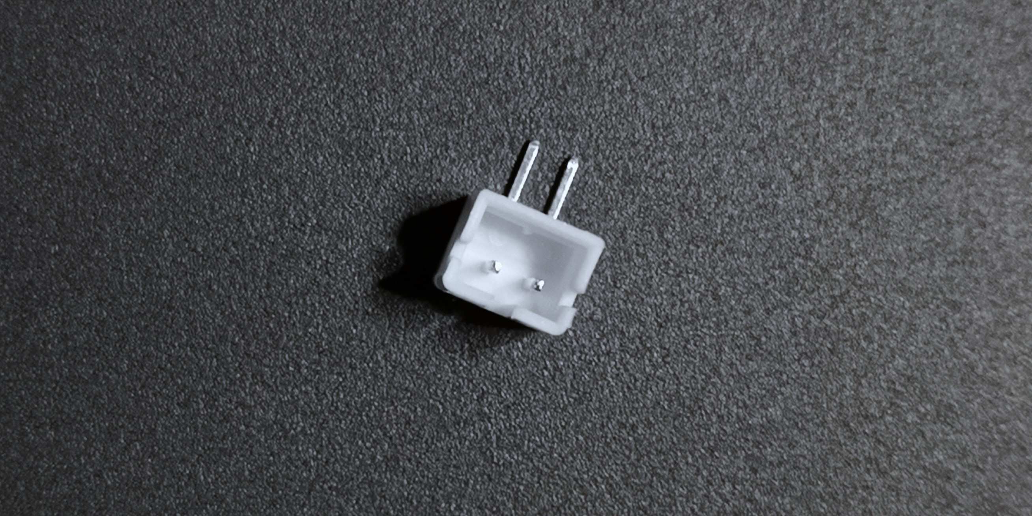
Misc/Assembly/Step-5-2Pin/1.jpg
