Aeurias/NadeshikoSlimeVR/Misc/Assembly/Step-5-2Pin/2mono.jpg

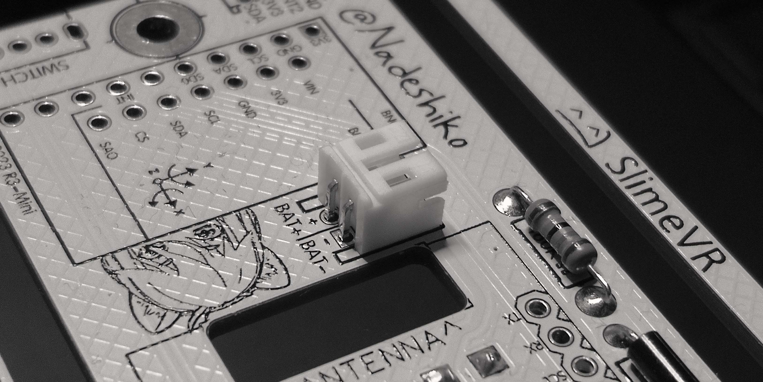
Misc/Assembly/Step-5-2Pin/2mono.jpg
