Aeurias/NadeshikoSlimeVR/Misc/Assembly/Step-5-2Pin/3mono.jpg

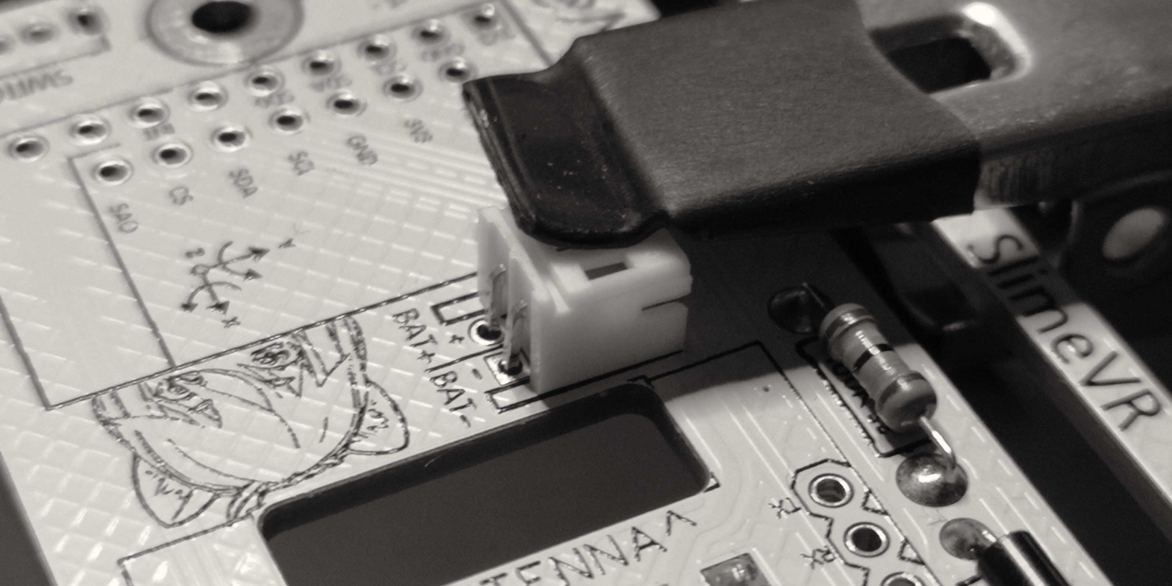
Misc/Assembly/Step-5-2Pin/3mono.jpg
