Aeurias/NadeshikoSlimeVR/Misc/Assembly/Step-5-2Pin/4mono.jpg

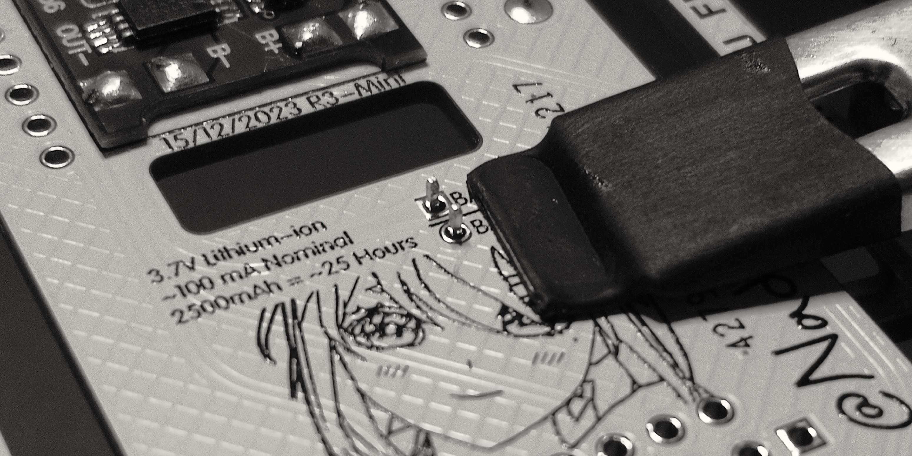
Misc/Assembly/Step-5-2Pin/4mono.jpg
