Aeurias/NadeshikoSlimeVR/Misc/Assembly/Step-5-2Pin/5.jpg

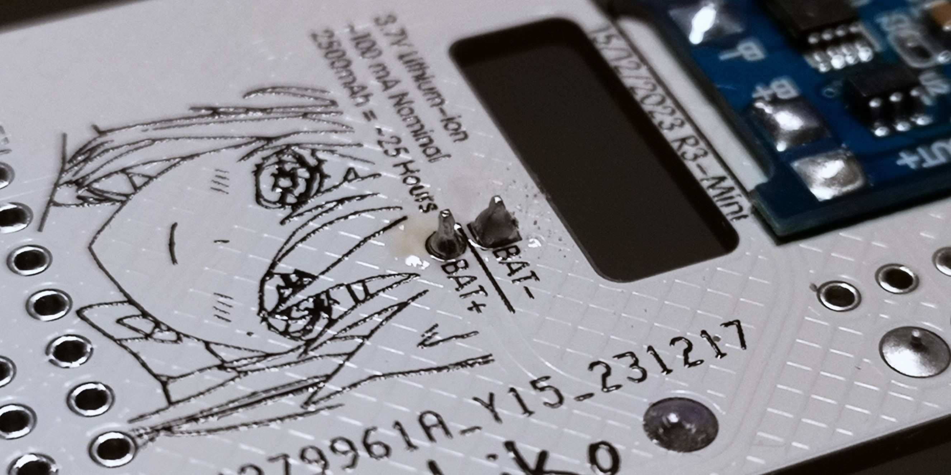
Misc/Assembly/Step-5-2Pin/5.jpg
