Aeurias/NadeshikoSlimeVR/Misc/Assembly/Step-5-2Pin/6.jpg

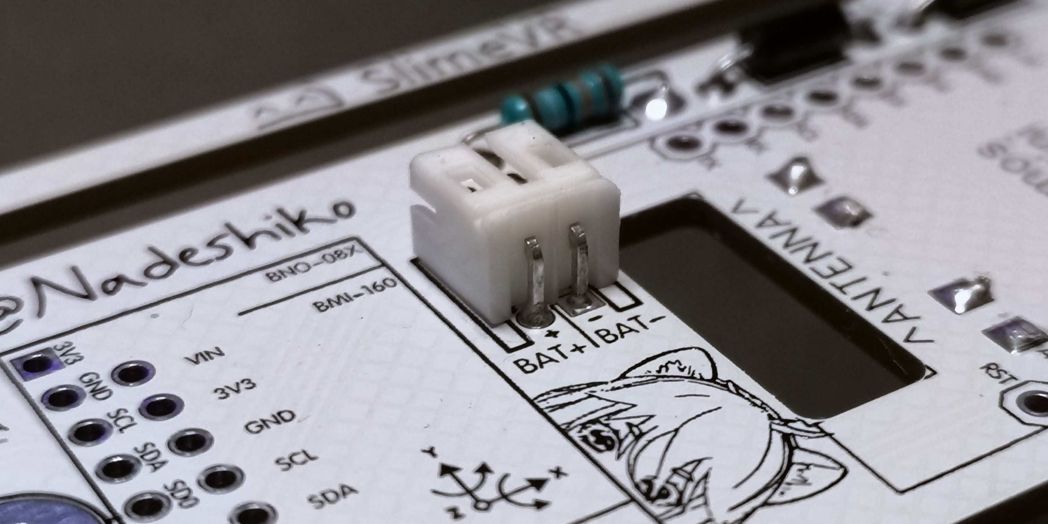
Misc/Assembly/Step-5-2Pin/6.jpg
