Aeurias/NadeshikoSlimeVR/Misc/Assembly/Step-6-5Pin-Switch/1.jpg

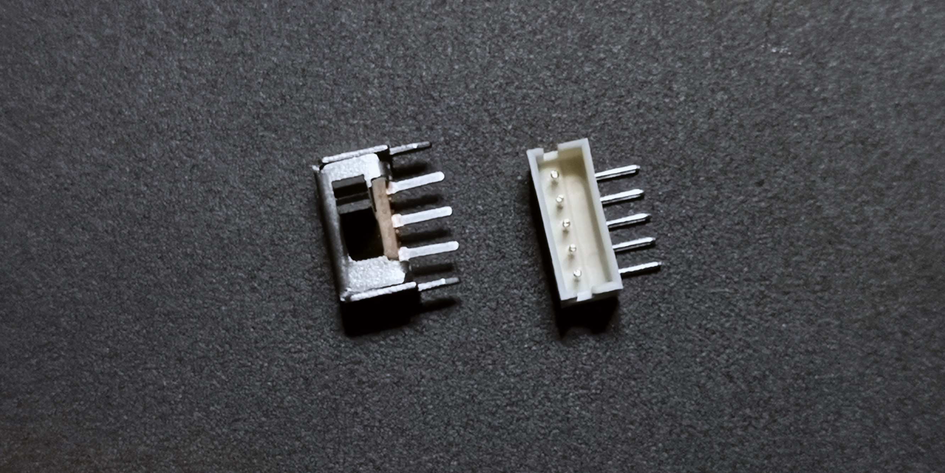
Misc/Assembly/Step-6-5Pin-Switch/1.jpg
