Aeurias/NadeshikoSlimeVR/Misc/Assembly/Step-6-5Pin-Switch/2mono.jpg

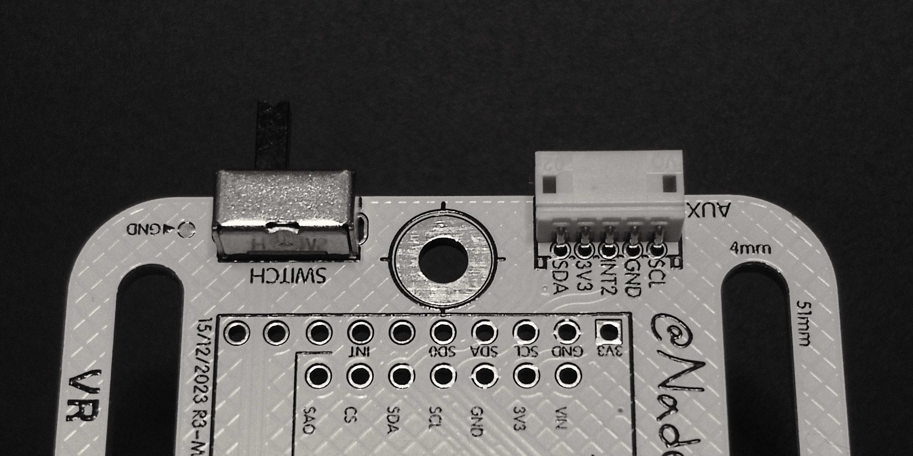
Misc/Assembly/Step-6-5Pin-Switch/2mono.jpg
