Aeurias/NadeshikoSlimeVR/Misc/Assembly/Step-6-5Pin-Switch/3mono.jpg

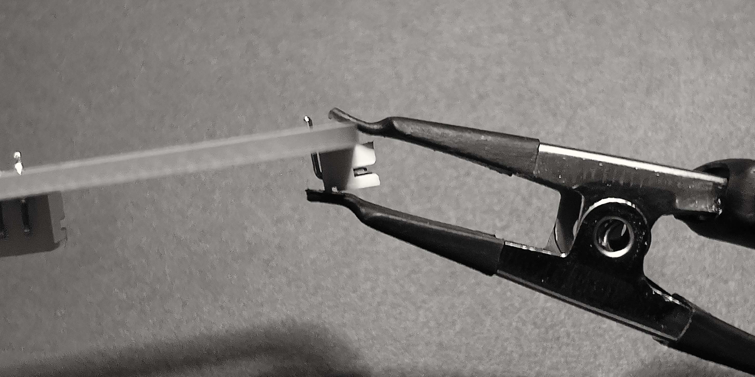
Misc/Assembly/Step-6-5Pin-Switch/3mono.jpg
