Aeurias/NadeshikoSlimeVR/Misc/Assembly/Step-6-5Pin-Switch/4mono.jpg

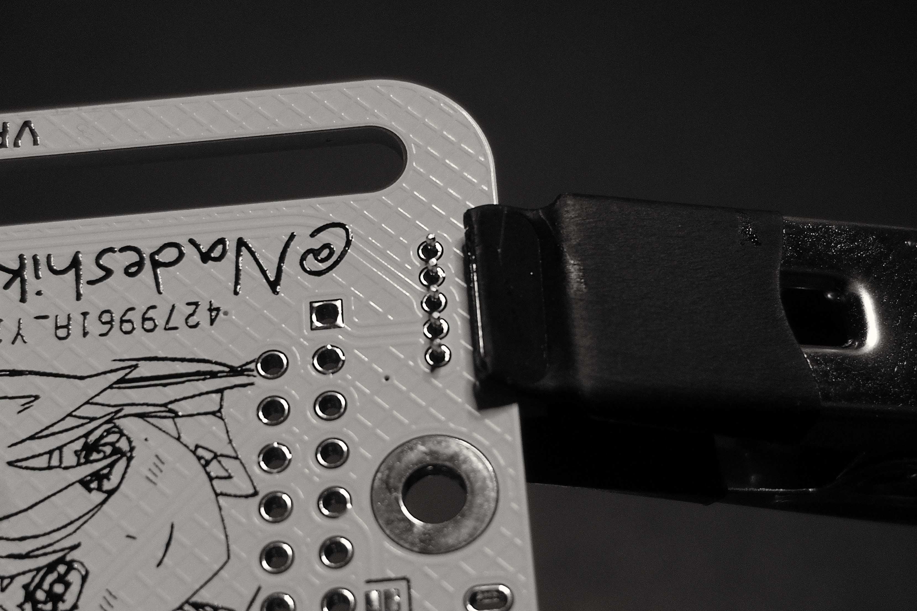
Misc/Assembly/Step-6-5Pin-Switch/4mono.jpg
