Aeurias/NadeshikoSlimeVR/Misc/Assembly/Step-6-5Pin-Switch/5.jpg

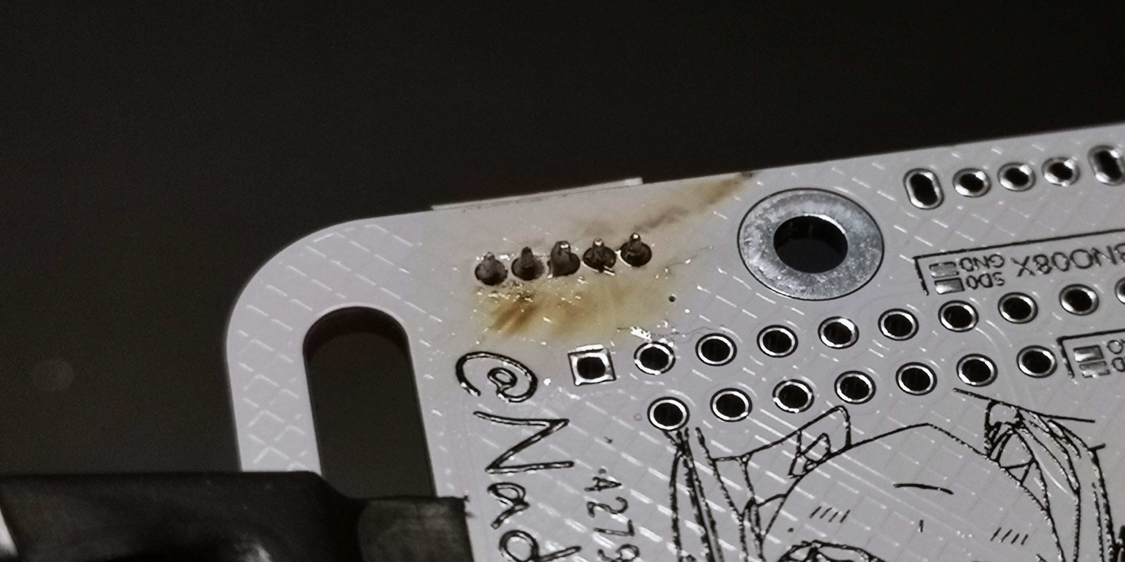
Misc/Assembly/Step-6-5Pin-Switch/5.jpg
