Aeurias/NadeshikoSlimeVR/Misc/Assembly/Step-6-5Pin-Switch/6mono.jpg

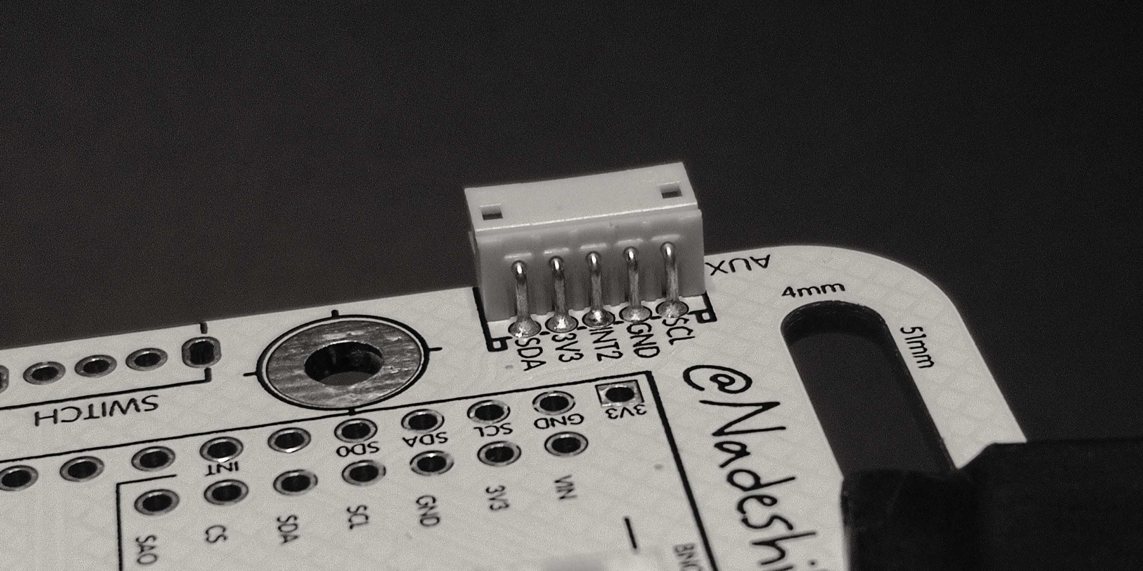
Misc/Assembly/Step-6-5Pin-Switch/6mono.jpg
