Aeurias/NadeshikoSlimeVR/Misc/Assembly/Step-6-5Pin-Switch/7mono.jpg

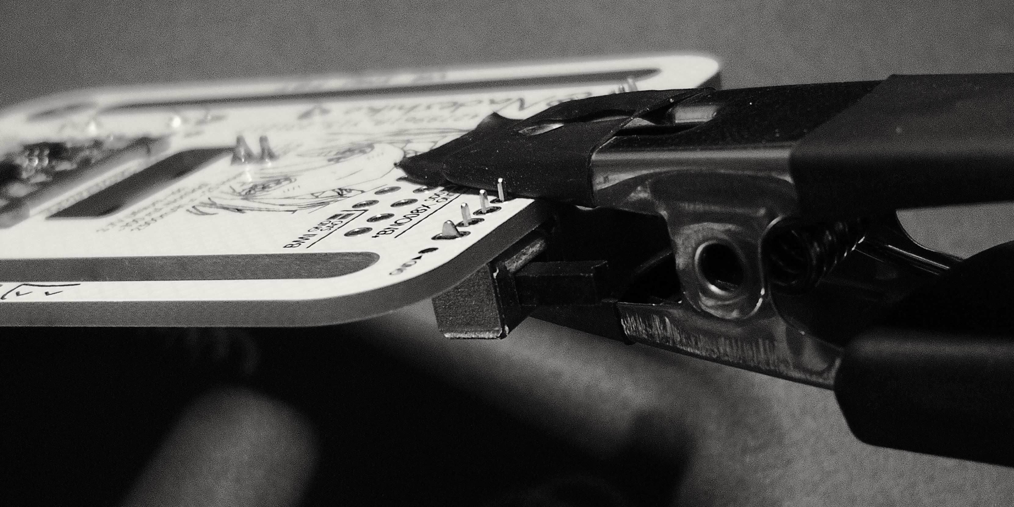
Misc/Assembly/Step-6-5Pin-Switch/7mono.jpg
