Aeurias/NadeshikoSlimeVR/Misc/Assembly/Step-6-5Pin-Switch/8mono.jpg

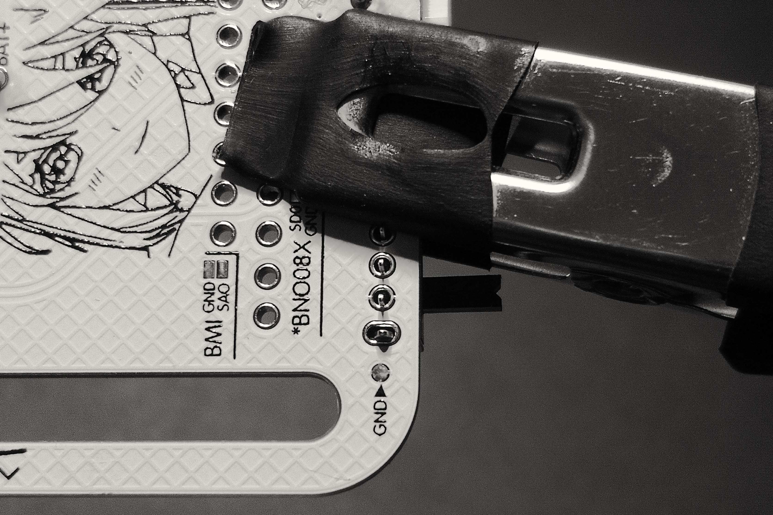
Misc/Assembly/Step-6-5Pin-Switch/8mono.jpg
