Aeurias/NadeshikoSlimeVR/Misc/Assembly/Step-6-5Pin-Switch/10.jpg

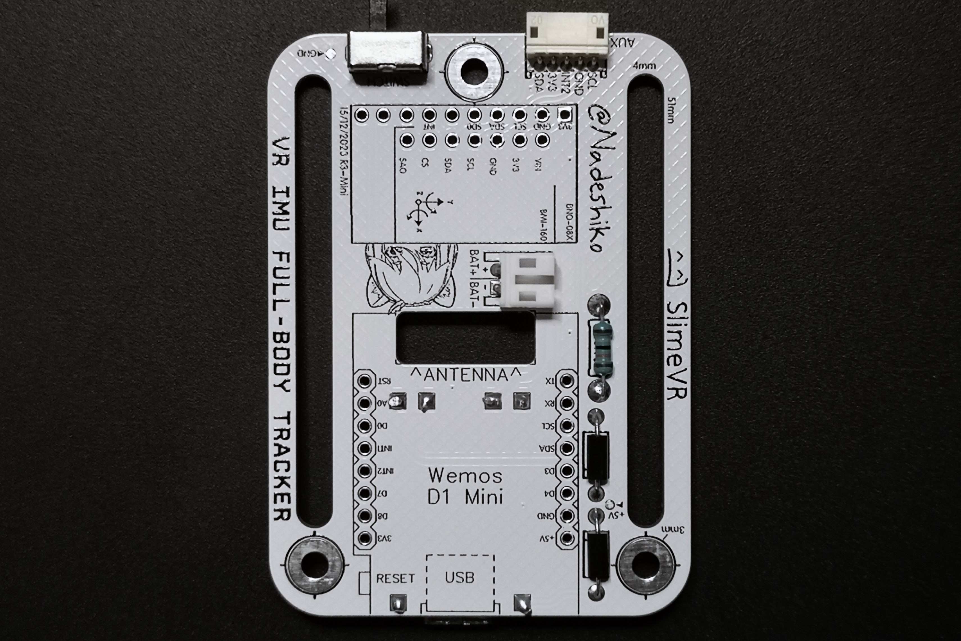
Misc/Assembly/Step-6-5Pin-Switch/10.jpg
