Aeurias/NadeshikoSlimeVR/Misc/Assembly/Step-6-5Pin-Switch/11.jpg

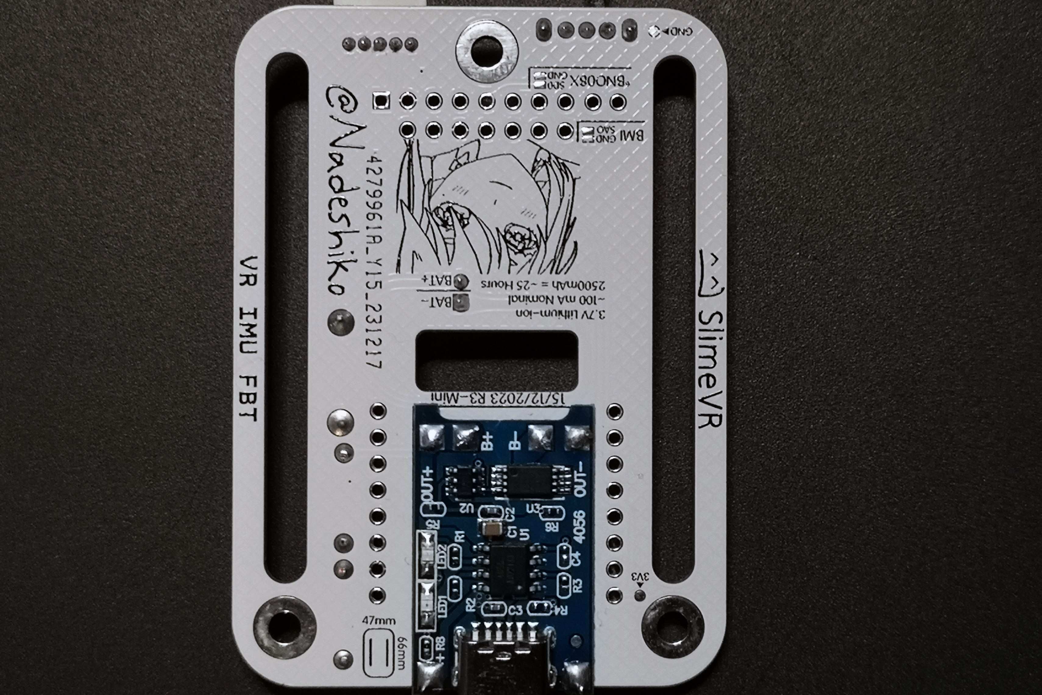
Misc/Assembly/Step-6-5Pin-Switch/11.jpg
