Aeurias/NadeshikoSlimeVR/Misc/Assembly/Step-7-BMI-BNO/0.jpg

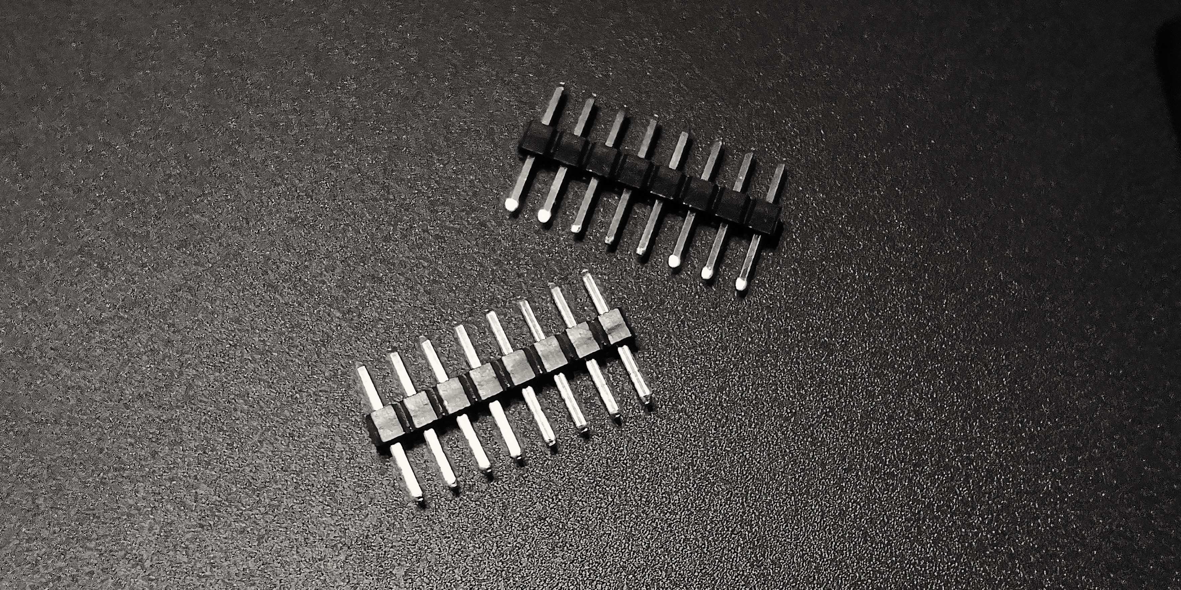
Misc/Assembly/Step-7-BMI-BNO/0.jpg
