Aeurias/NadeshikoSlimeVR/Misc/Assembly/Step-7-BMI-BNO/1.jpg

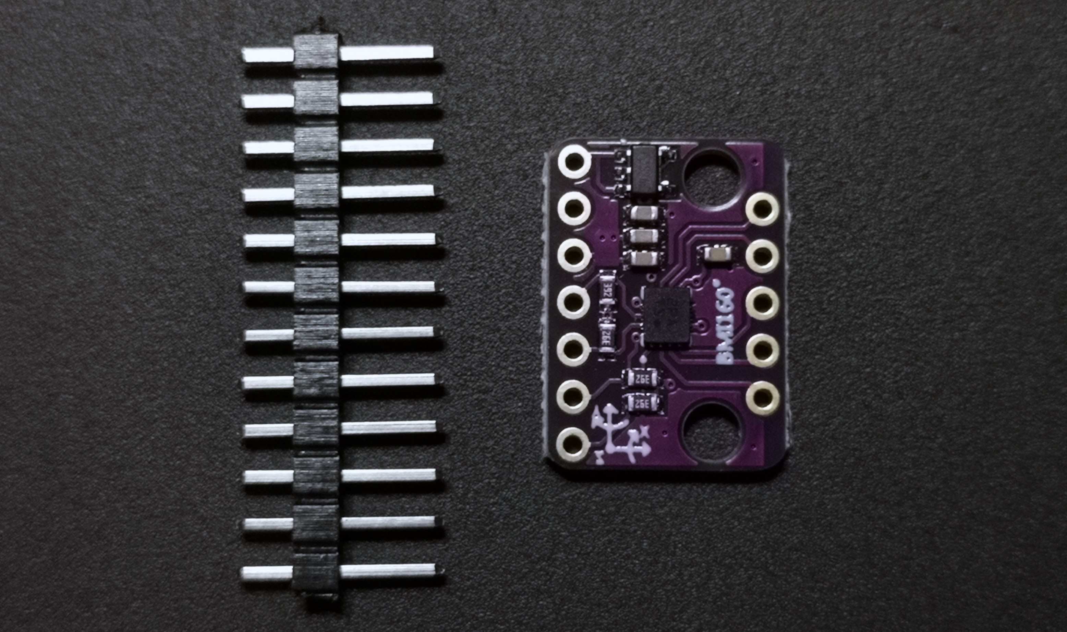
Misc/Assembly/Step-7-BMI-BNO/1.jpg
