Aeurias/NadeshikoSlimeVR/Misc/Assembly/Step-7-BMI-BNO/2.jpg

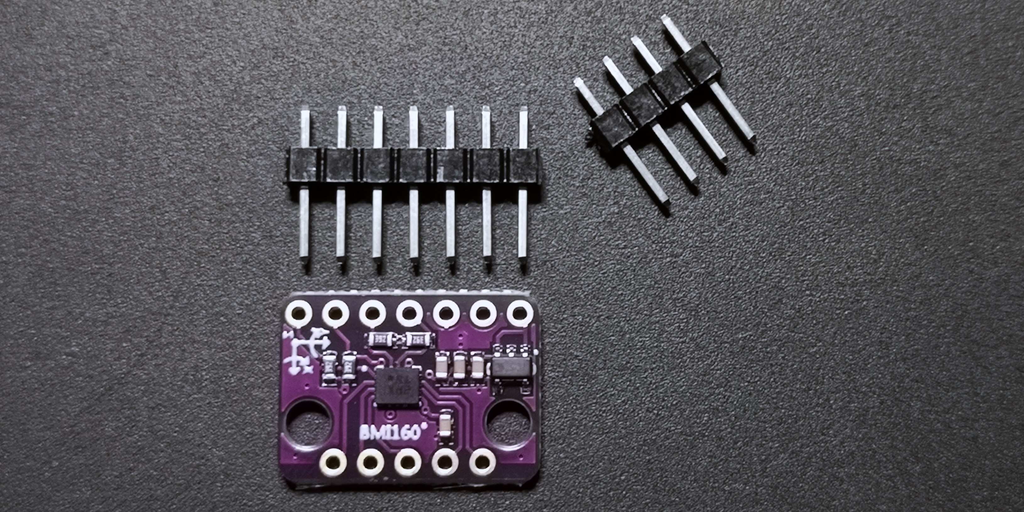
Misc/Assembly/Step-7-BMI-BNO/2.jpg
