Aeurias/NadeshikoSlimeVR/Misc/Assembly/Step-7-BMI-BNO/4.jpg

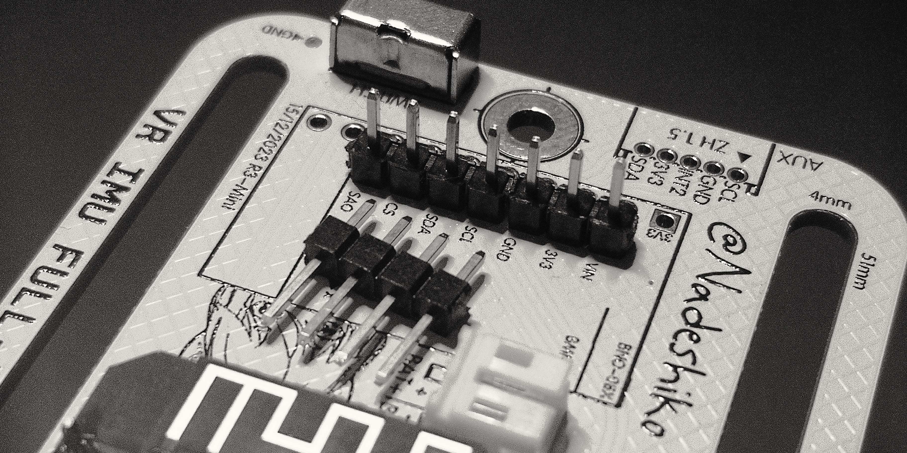
Misc/Assembly/Step-7-BMI-BNO/4.jpg
