Aeurias/NadeshikoSlimeVR/Misc/Assembly/Step-7-BMI-BNO/5.jpg

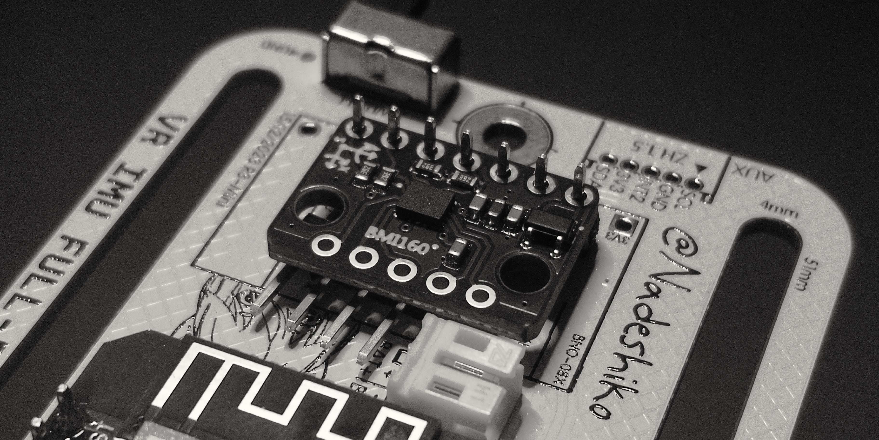
Misc/Assembly/Step-7-BMI-BNO/5.jpg
