Aeurias/NadeshikoSlimeVR/Misc/Assembly/Step-7-BMI-BNO/6.jpg

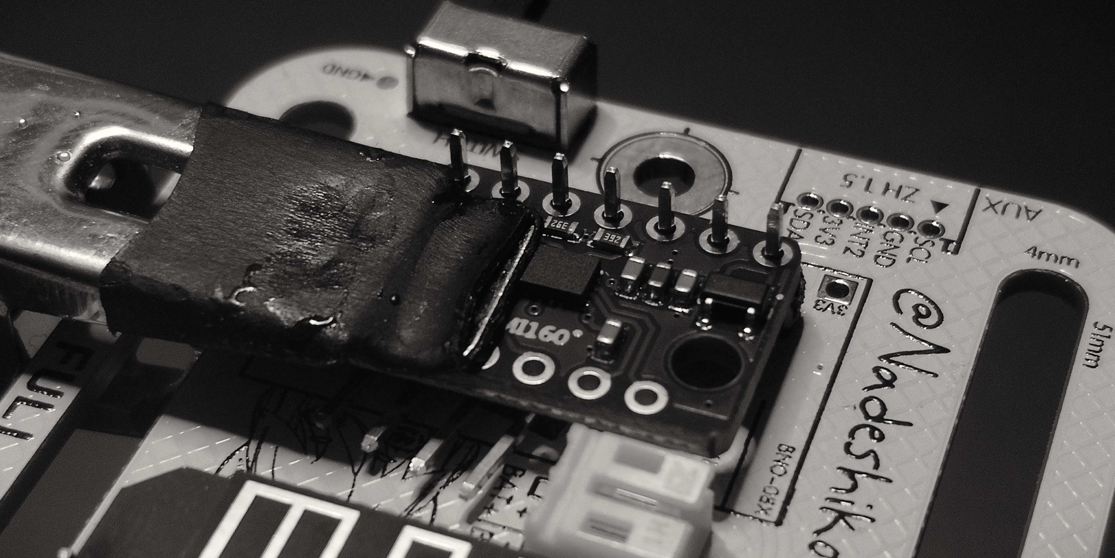
Misc/Assembly/Step-7-BMI-BNO/6.jpg
