Aeurias/NadeshikoSlimeVR/Misc/Assembly/Step-7-BMI-BNO/7.jpg

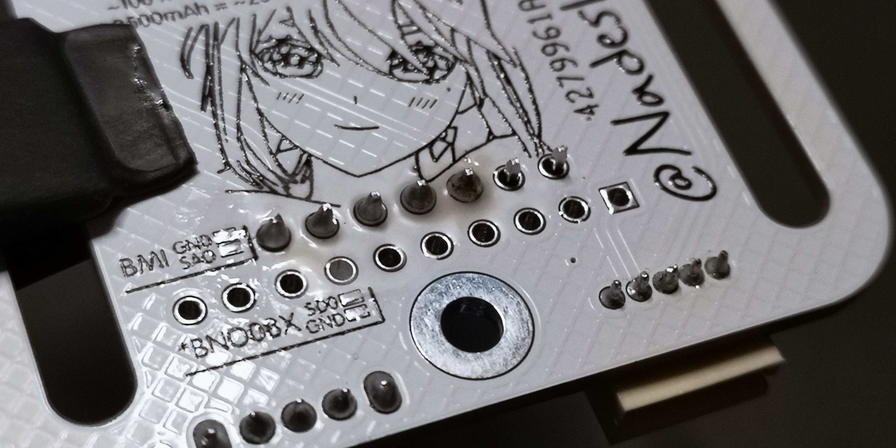
Misc/Assembly/Step-7-BMI-BNO/7.jpg
