Aeurias/NadeshikoSlimeVR/Misc/Assembly/Step-7-BMI-BNO/12mono.jpg

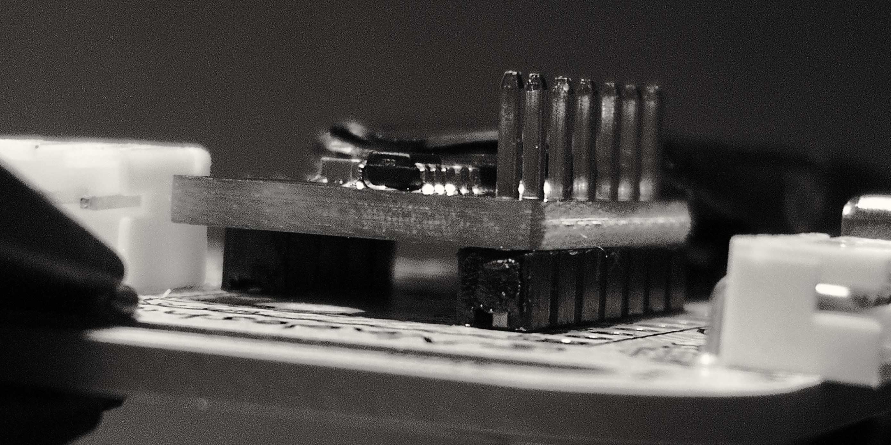
Misc/Assembly/Step-7-BMI-BNO/12mono.jpg
