Aeurias/NadeshikoSlimeVR/Misc/Assembly/Step-7-BMI-BNO/13.jpg

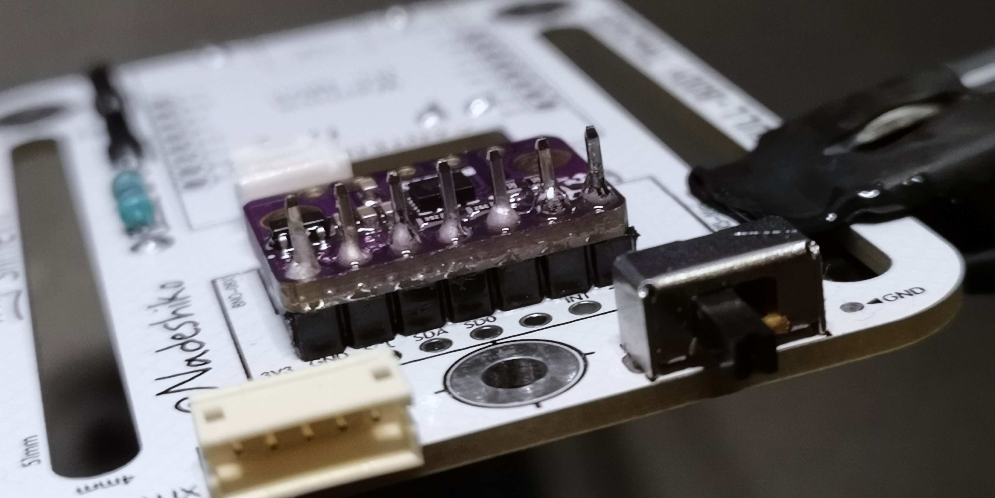
Misc/Assembly/Step-7-BMI-BNO/13.jpg
