Aeurias/NadeshikoSlimeVR/Misc/Assembly/Step-8-D1Mini/1.jpg

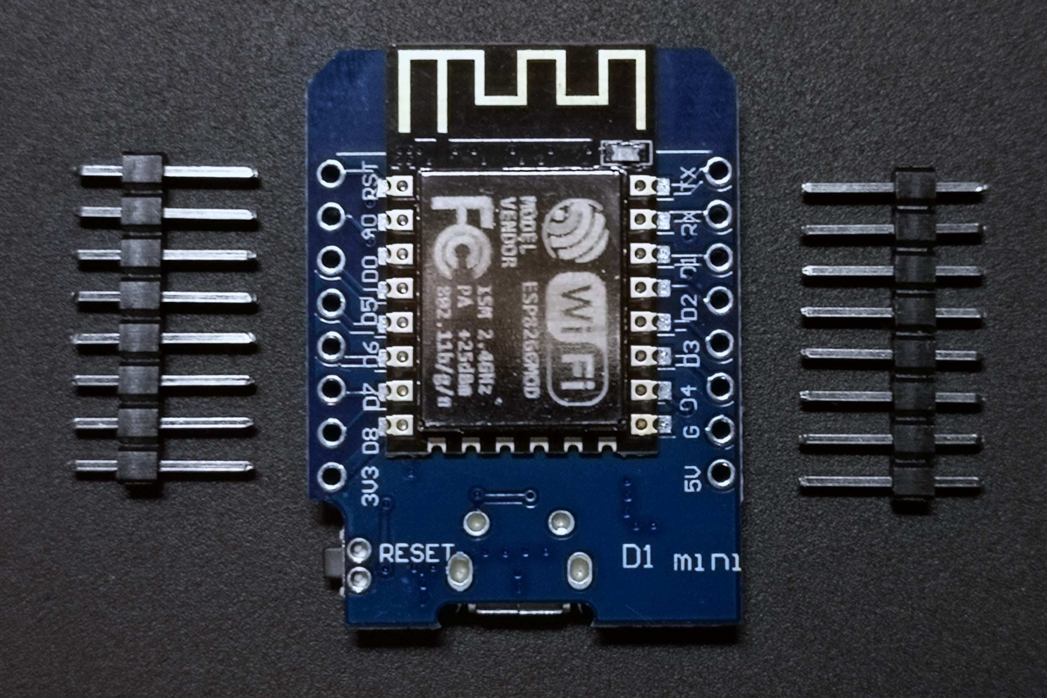
Misc/Assembly/Step-8-D1Mini/1.jpg
