Aeurias/NadeshikoSlimeVR/Misc/Assembly/Step-8-D1Mini/2.jpg

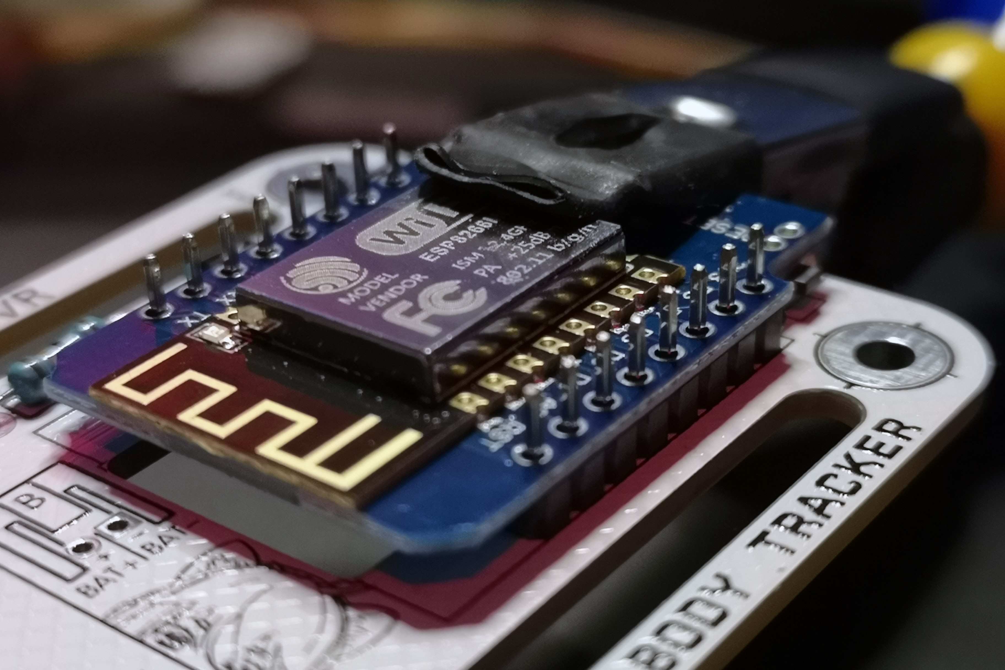
Misc/Assembly/Step-8-D1Mini/2.jpg
