Aeurias/NadeshikoSlimeVR/Misc/Assembly/Step-8-D1Mini/3.jpg

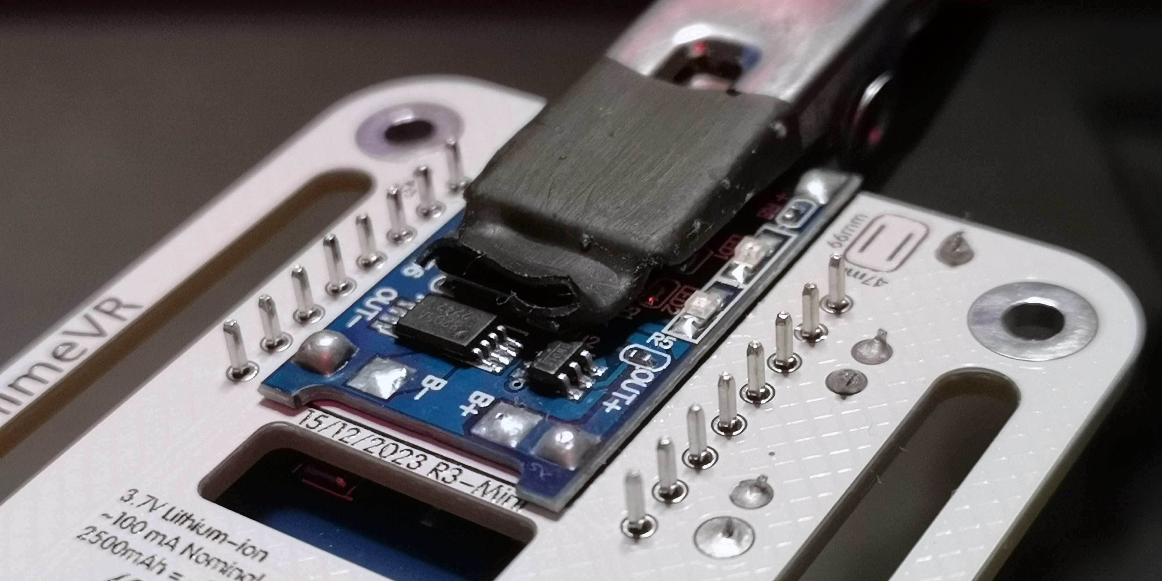
Misc/Assembly/Step-8-D1Mini/3.jpg
