Aeurias/NadeshikoSlimeVR/Misc/Assembly/Step-8-D1Mini/4.jpg

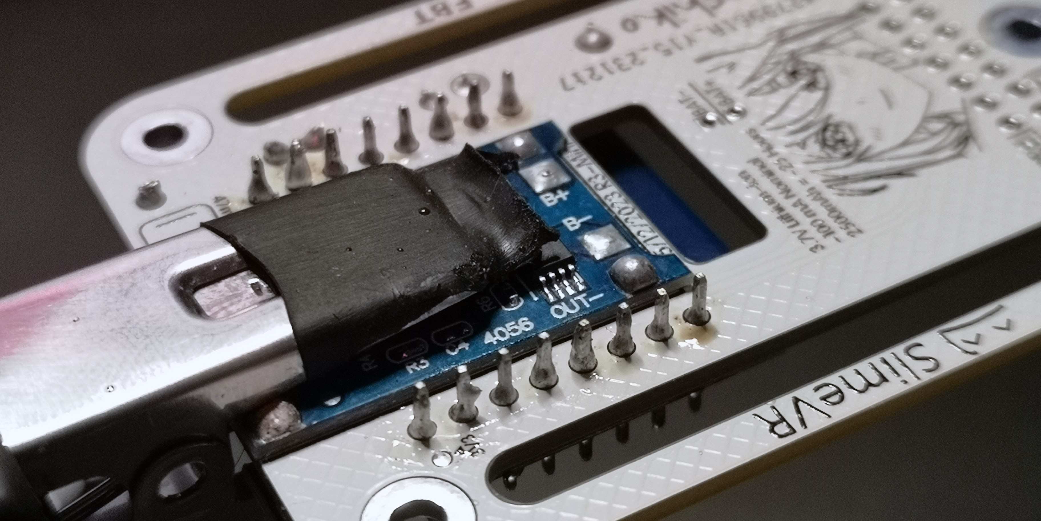
Misc/Assembly/Step-8-D1Mini/4.jpg
