Aeurias/NadeshikoSlimeVR/Misc/Assembly/Step-8-D1Mini/5.jpg

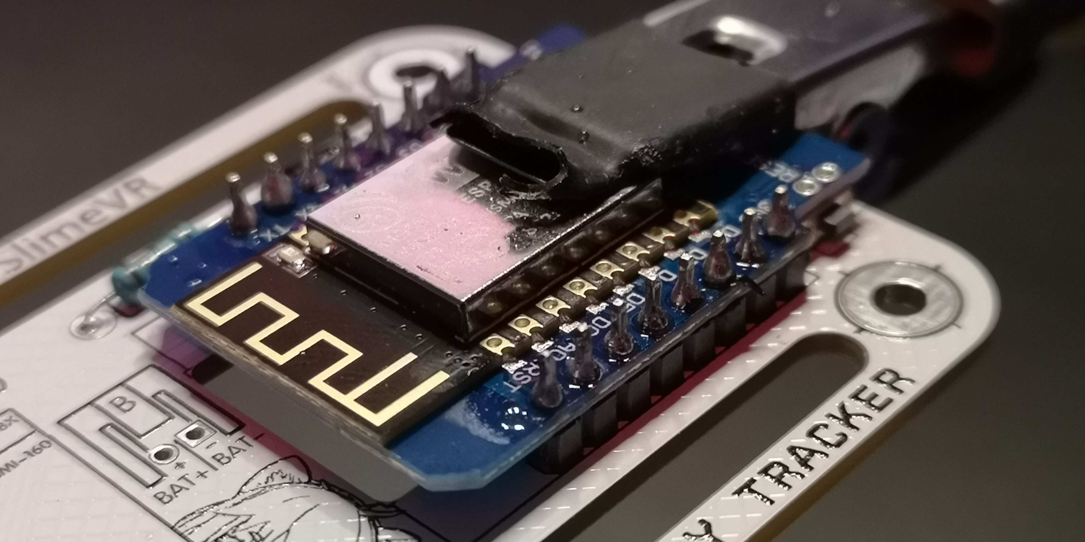
Misc/Assembly/Step-8-D1Mini/5.jpg
