Aeurias/NadeshikoSlimeVR/Misc/Assembly/Step-8-D1Mini/6.jpg

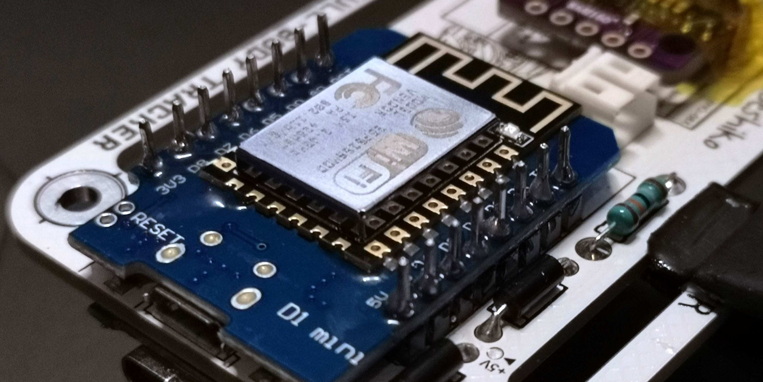
Misc/Assembly/Step-8-D1Mini/6.jpg
