Aeurias/NadeshikoSlimeVR/Misc/Assembly/Step-9-Cleaned/1.jpg

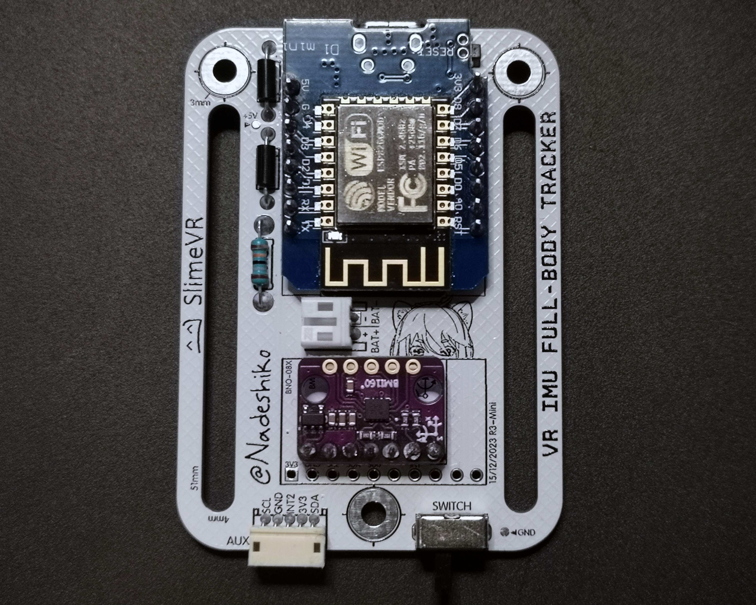
Misc/Assembly/Step-9-Cleaned/1.jpg
