Aeurias/NadeshikoSlimeVR/Misc/Assembly/Step-9-Cleaned/2.jpg

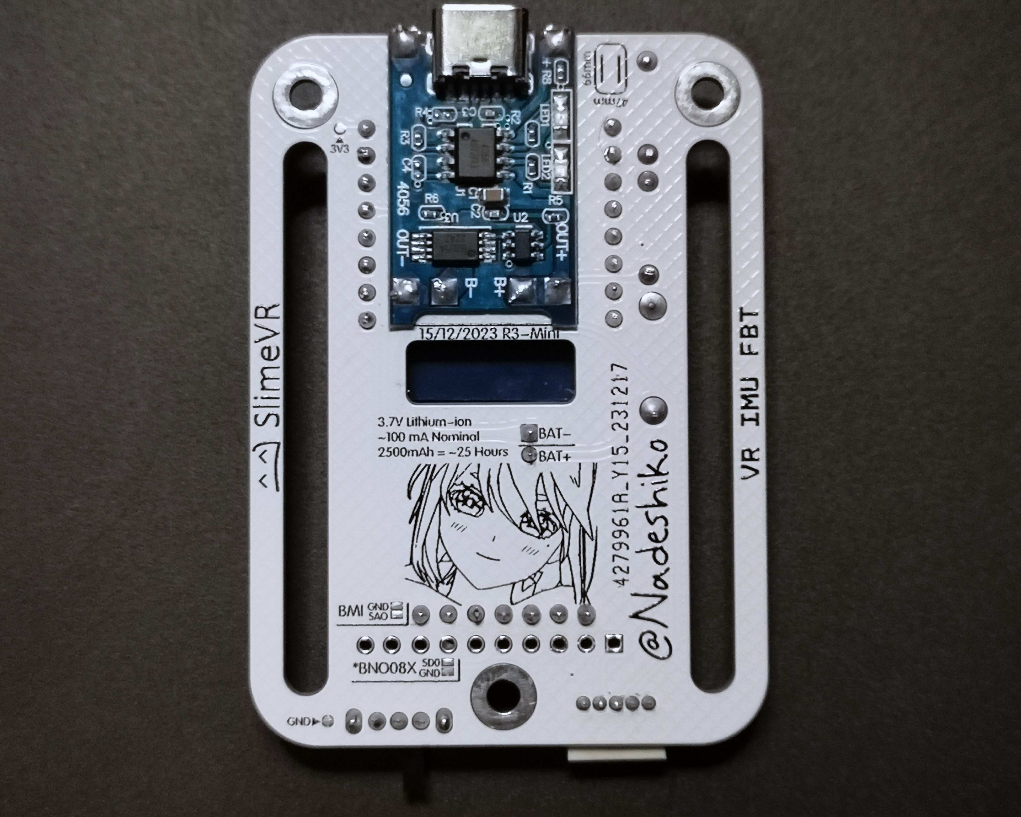
Misc/Assembly/Step-9-Cleaned/2.jpg
