Aeurias/NadeshikoSlimeVR/Misc/Assembly/Step-10-Tape/1.jpg

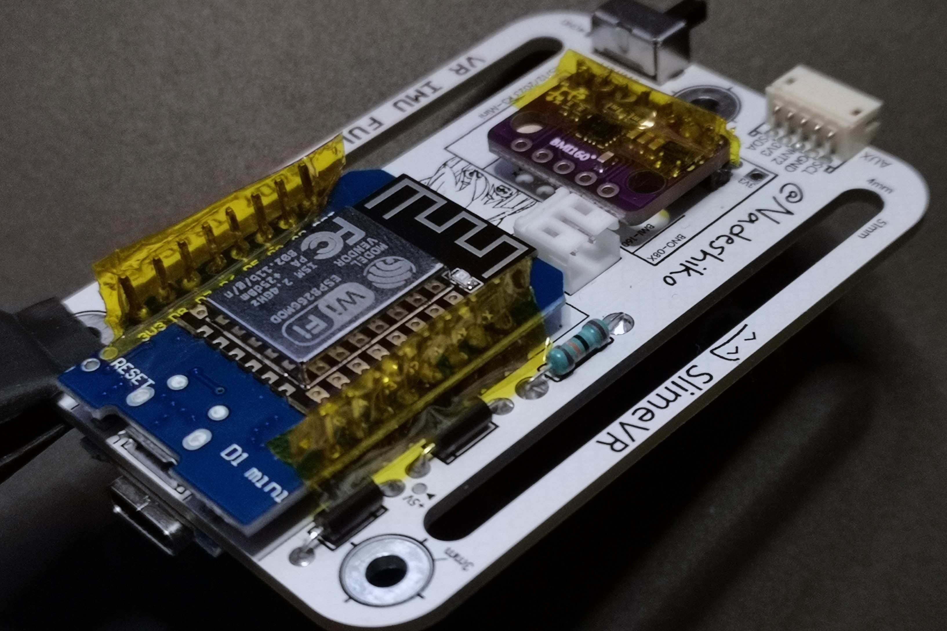
Misc/Assembly/Step-10-Tape/1.jpg
