Aeurias/NadeshikoSlimeVR/Misc/Assembly/Step-10-Tape/3.jpg

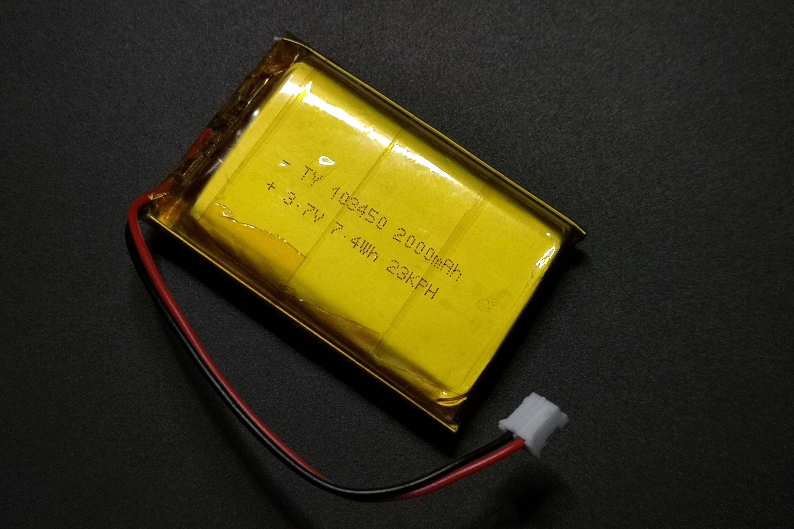
Misc/Assembly/Step-10-Tape/3.jpg
