Aeurias/NadeshikoSlimeVR/Tracker Supermini/3D Print STL/WallThicknessWarning.png

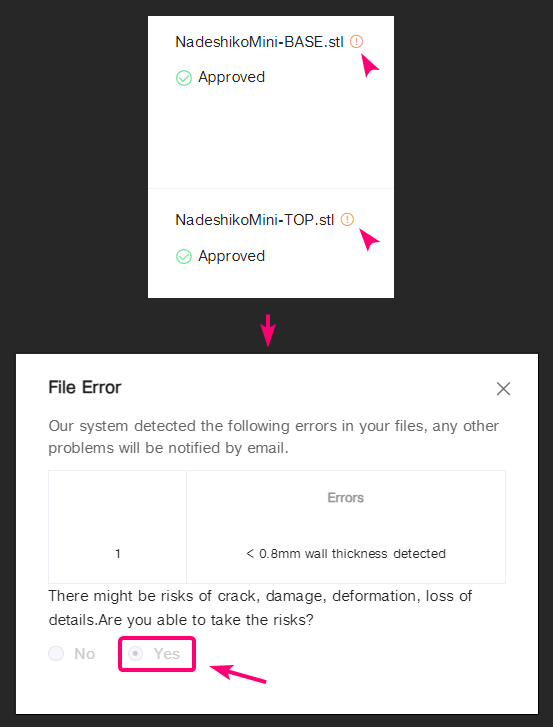
Tracker Supermini/3D Print STL/WallThicknessWarning.png
